ataweg/aweAvrSynth/PCB/Mainboard/avrsynth.sch

## KiCad design PCB/Mainboard/avrsynth.sch (2012-10-20)

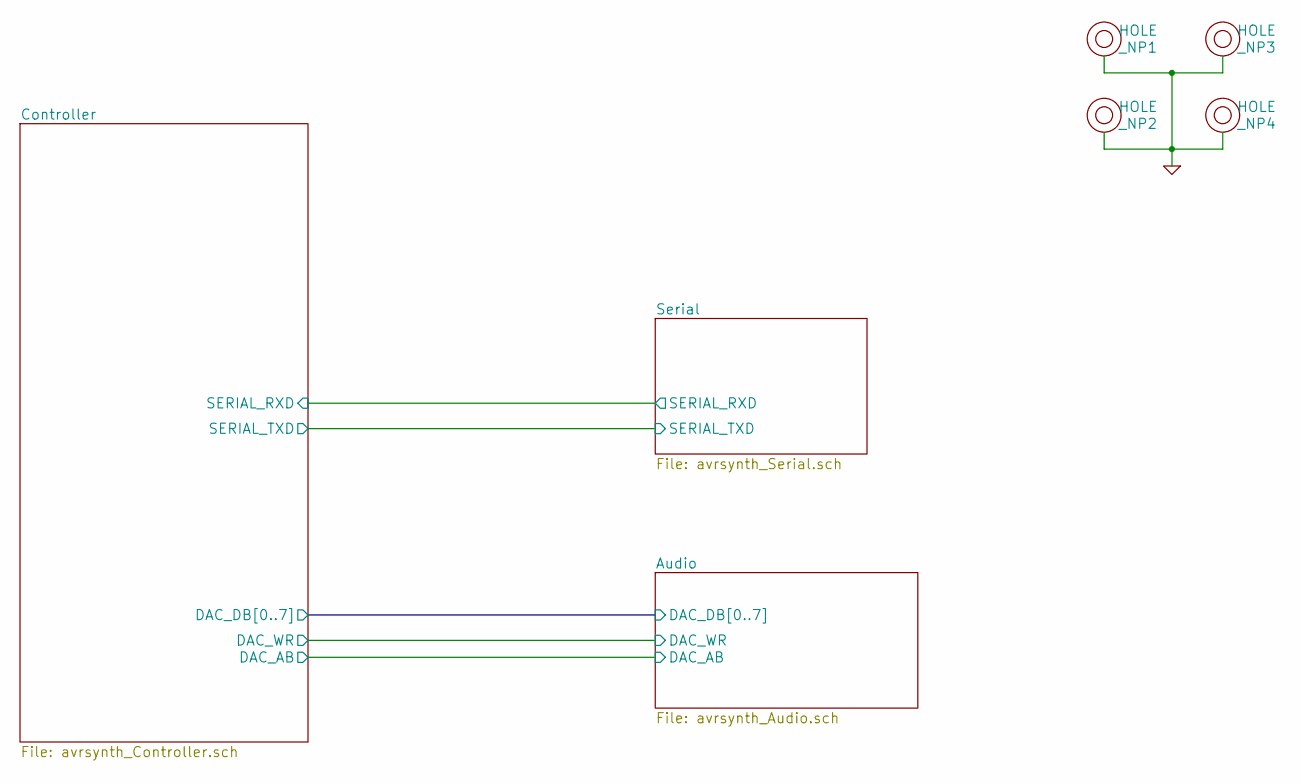
[picture p12: schematic avrsynth.sch]

Parts:
_NP1, _NP2, _NP3, _NP4: HOLE; HOLE_32

Connections:
GND: _NP1.1, _NP2.1, _NP3.1, _NP4.1
