ataweg/aweAvrSynth/PCB/Mainboard/avrsynth_Audio.sch

## KiCad design PCB/Mainboard/avrsynth_Audio.sch (2012-10-20)

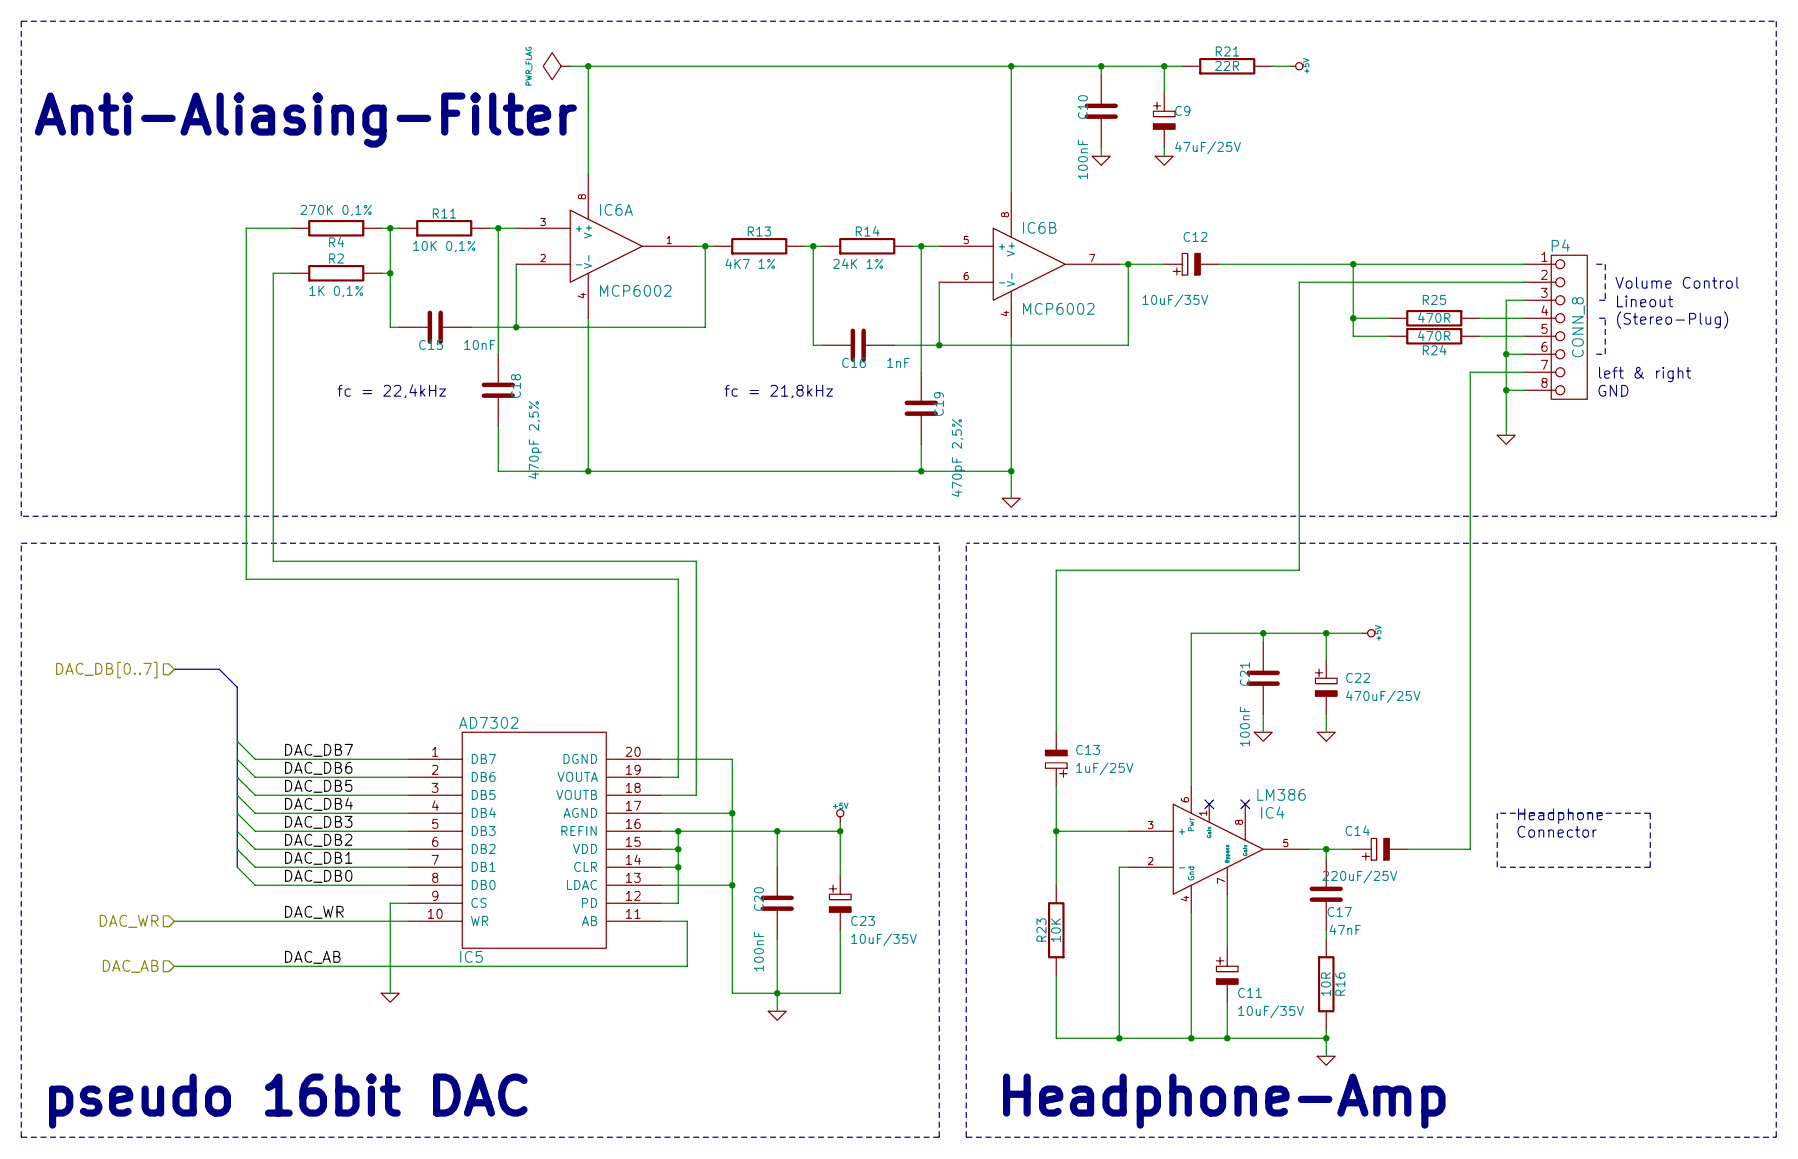
[picture p13: schematic avrsynth_Audio.sch]

Parts:
C9: 47uF/25V; C1V5
C10, C20, C21: 100nF; C2
C11, C12, C23: 10uF/35V; C1V5
C13: 1uF/25V; C1V5
C14: 220uF/25V; C2V8
C15: 10nF; C2
C16: 1nF; C2
C17: 47nF; C2
C18, C19: 470pF 2,5%; C2
C22: 470uF/25V; C2V10
IC4: LM386; DIP-8__300
IC5: AD7302; DIP-20__300
IC6: MCP6002; DIP-8__300
P4: CONN_8; PS25_8G
R2: 1K 0,1%; R4
R4: 270K 0,1%; R4
R11: 10K 0,1%; R4
R13: 4K7 1%; R4
R14: 24K 1%; R4
R16: 10R; R4
R21: 22R; R4
R23: 10K; R4
R24, R25: 470R; R4

Connections:
+5V: C20.2, C21.2, C22.2 (+), C23.2 (+), IC4.6 (Pwr), IC5.12 (PD), IC5.14 (CLR), IC5.15 (VDD), IC5.16 (REFIN), R21.2
DAC_AB: IC5.11 (AB)
DAC_DB0: IC5.8 (DB0)
DAC_DB1: IC5.7 (DB1)
DAC_DB2: IC5.6 (DB2)
DAC_DB3: IC5.5 (DB3)
DAC_DB4: IC5.4 (DB4)
DAC_DB5: IC5.3 (DB5)
DAC_DB6: IC5.2 (DB6)
DAC_DB7: IC5.1 (DB7)
DAC_WR: IC5.10 (WR)
GND: C9.1 (-), C10.1, C11.1 (-), C18.1, C19.1, C20.1, C21.1, C22.1 (-), C23.1 (-), IC4.2 (-), IC4.4 (Gnd), IC5.9 (CS), IC5.13 (LDAC), IC5.17 (AGND), IC5.20 (DGND), IC6.4 (V-), P4.3, P4.6, P4.8, R16.2, R23.1
unnamed: C9.2 (+), C10.2, IC6.8 (V+), R21.1
unnamed: C11.2 (+), IC4.7 (Bypass)
unnamed: C12.1 (-), P4.1, R24.2, R25.2
unnamed: C12.2 (+), C16.1, IC6.6 (-), IC6.7
unnamed: C13.1 (-), P4.2
unnamed: C13.2 (+), IC4.3 (+), R23.2
unnamed: C14.1 (-), P4.7
unnamed: C14.2 (+), C17.2, IC4.5
unnamed: C15.1, IC6.1, IC6.2 (-), R13.1
unnamed: C15.2, R2.2, R4.1, R11.1
unnamed: C16.2, R13.2, R14.1
unnamed: C17.1, R16.1
unnamed: C18.2, IC6.3 (+), R11.2
unnamed: C19.2, IC6.5 (+), R14.2
unnamed: IC5.18 (VOUTB), R2.1
unnamed: IC5.19 (VOUTA), R4.2
unnamed: P4.4, R25.1
unnamed: P4.5, R24.1

Notes on the sheet:
fc = 21,8kHz
fc = 22,4kHz
Headphone Connector
left & right
GND
Headphone-Amp
pseudo 16bit DAC
Anti-Aliasing-Filter
Volume Control
Lineout (Stereo-Plug)
