ataweg/aweAvrSynth/PCB/Mainboard/avrsynth_Controller.sch

## KiCad design PCB/Mainboard/avrsynth_Controller.sch (2012-10-20)

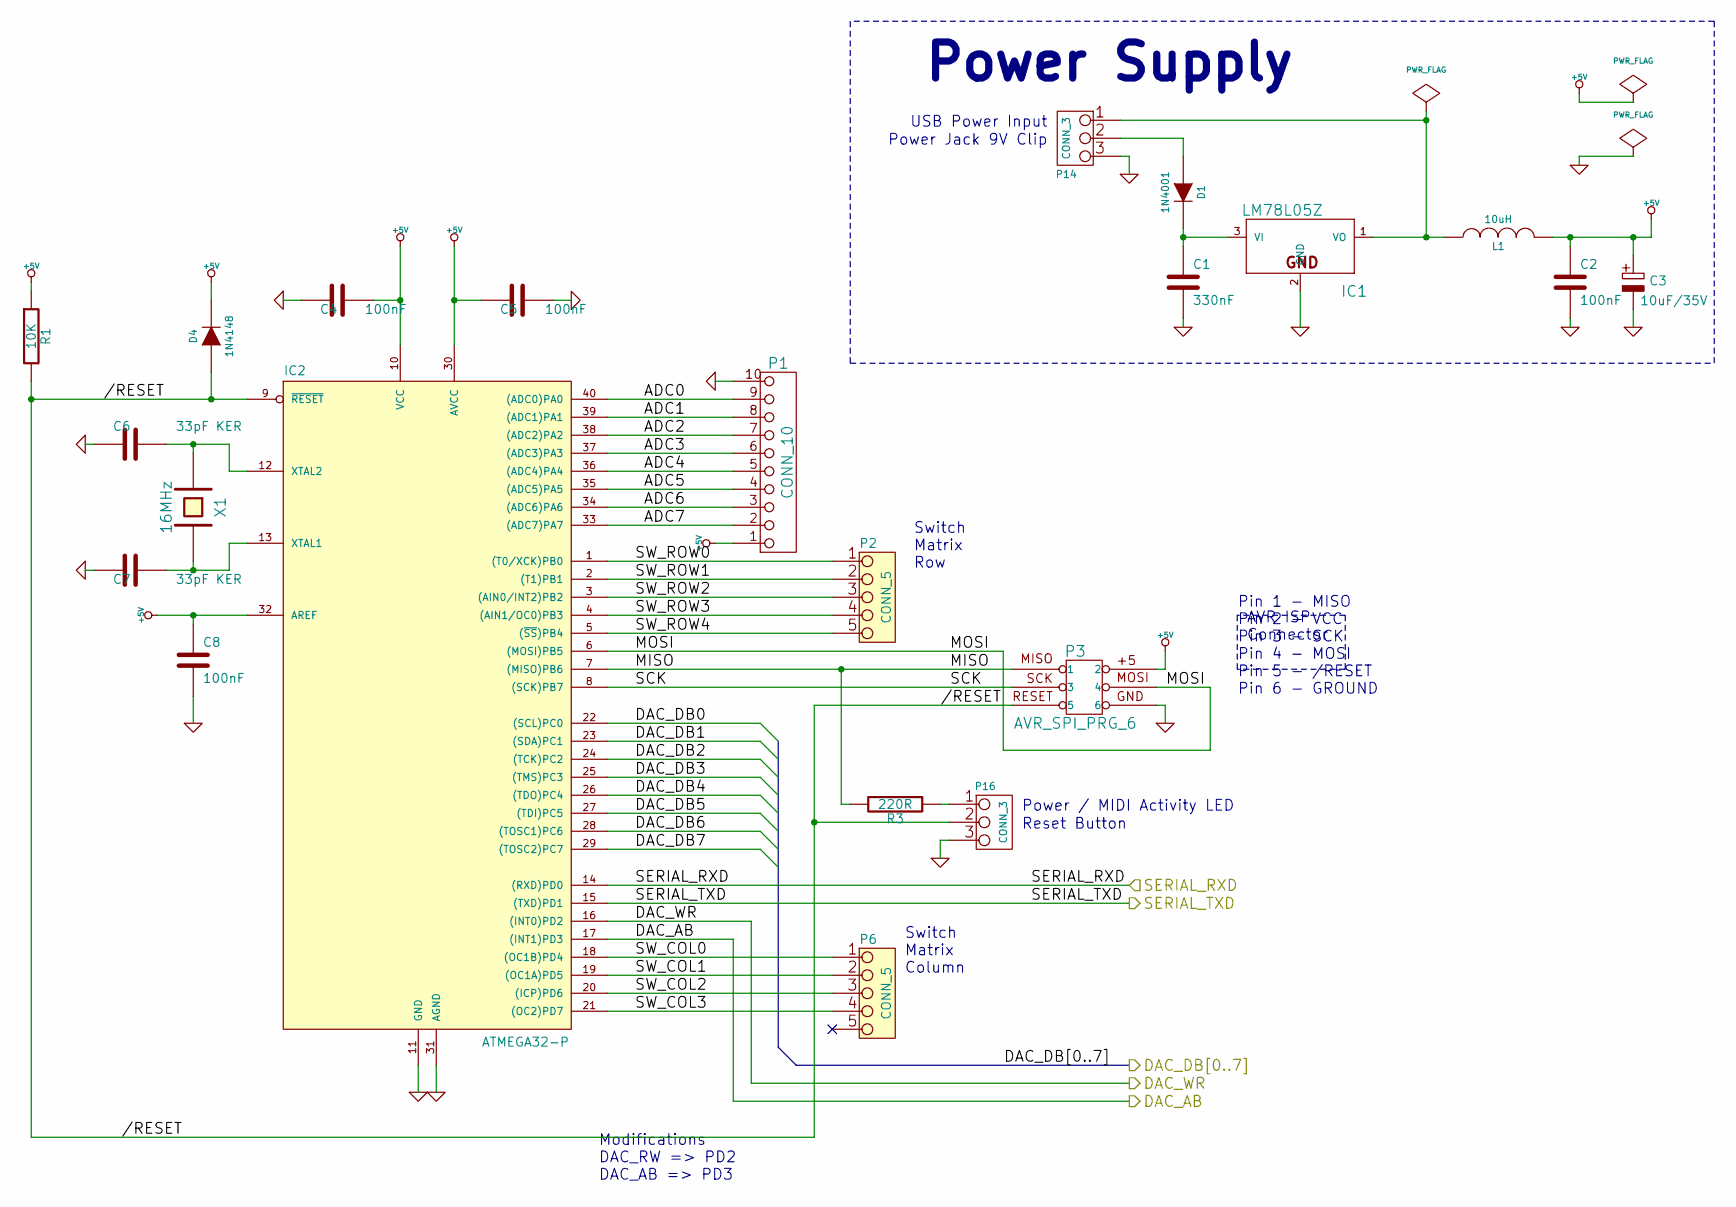
[picture p14: schematic avrsynth_Controller.sch]

Parts:
C1: 330nF; C2
C2: 100nF; C2
C3: 10uF/35V; C1V5
C4, C5, C8: 100nF; C1
C6, C7: 33pF KER; C1
D1: 1N4001; DO41-4
D4: 1N4148; DO35-3
IC1: LM78L05Z; TO92-123
IC2: ATMEGA32-P; DIP-40__600
L1: 10uH; R5
P1: CONN_10; PS25_10G
P2, P6: CONN_5; PS25_5G
P3: AVR_SPI_PRG_6
P14, P16: CONN_3; PS25_3G
R1: 10K; R4
R3: 220R; R4
X1: 16MHz; HC-49V

Connections:
+5V: C2.1, C3.2 (+), C4.1, C5.2, C8.1, D4.2 (K), IC2.10 (VCC), IC2.30 (AVCC), IC2.32 (AREF), L1.2, P1.1, P3.2, R1.1
/RESET: D4.1 (A), IC2.9 (~RESET), P3.5, P16.2 (PM), R1.2
ADC0: IC2.40 ((ADC0)PA0), P1.9
ADC1: IC2.39 ((ADC1)PA1), P1.8
ADC2: IC2.38 ((ADC2)PA2), P1.7
ADC3: IC2.37 ((ADC3)PA3), P1.6
ADC4: IC2.36 ((ADC4)PA4), P1.5
ADC5: IC2.35 ((ADC5)PA5), P1.4
ADC6: IC2.34 ((ADC6)PA6), P1.3
ADC7: IC2.33 ((ADC7)PA7), P1.2
DAC_AB: IC2.17 ((INT1)PD3)
DAC_DB0: IC2.22 ((SCL)PC0)
DAC_DB1: IC2.23 ((SDA)PC1)
DAC_DB2: IC2.24 ((TCK)PC2)
DAC_DB3: IC2.25 ((TMS)PC3)
DAC_DB4: IC2.26 ((TDO)PC4)
DAC_DB5: IC2.27 ((TDI)PC5)
DAC_DB6: IC2.28 ((TOSC1)PC6)
DAC_DB7: IC2.29 ((TOSC2)PC7)
DAC_WR: IC2.16 ((INT0)PD2)
GND: C1.2, C2.2, C3.1 (-), C4.2, C5.1, C6.2, C7.2, C8.2, IC1.2 (GND), IC2.11 (GND), IC2.31 (AGND), P1.10, P3.6, P14.3, P16.3
MISO: IC2.7 ((MISO)PB6), P3.1, R3.2
MOSI: IC2.6 ((MOSI)PB5), P3.4
unnamed: C1.1, D1.2 (K), IC1.3 (VI)
unnamed: C6.1, IC2.12 (XTAL2), X1.1
unnamed: C7.1, IC2.13 (XTAL1), X1.2
unnamed: D1.1 (A), P14.2 (PM)
unnamed: IC1.1 (VO), L1.1, P14.1
unnamed: P16.1, R3.1
SCK: IC2.8 ((SCK)PB7), P3.3
SERIAL_RXD: IC2.14 ((RXD)PD0)
SERIAL_TXD: IC2.15 ((TXD)PD1)
SW_COL0: IC2.18 ((OC1B)PD4), P6.1
SW_COL1: IC2.19 ((OC1A)PD5), P6.2
SW_COL2: IC2.20 ((ICP)PD6), P6.3
SW_COL3: IC2.21 ((OC2)PD7), P6.4
SW_ROW0: IC2.1 ((T0/XCK)PB0), P2.1
SW_ROW1: IC2.2 ((T1)PB1), P2.2
SW_ROW2: IC2.3 ((AIN0/INT2)PB2), P2.3
SW_ROW3: IC2.4 ((AIN1/OC0)PB3), P2.4
SW_ROW4: IC2.5 ((~SS~)PB4), P2.5

Notes on the sheet:
Switch Matrix Column
Switch Matrix Row
Modifications DAC_RW => PD2 DAC_AB => PD3
Power / MIDI Activity LED
Reset Button
Power Supply
Power Jack 9V Clip
USB Power Input
Pin 1 - MISO Pin 2 - VCC Pin 3 - SCK Pin 4 - MOSI Pin 5 - /RESET Pin 6 - GROUND
AVR ISP Connector
