ataweg/aweAvrSynth/PCB/Mainboard/avrsynth_Serial.sch

## KiCad design PCB/Mainboard/avrsynth_Serial.sch (2012-10-20)

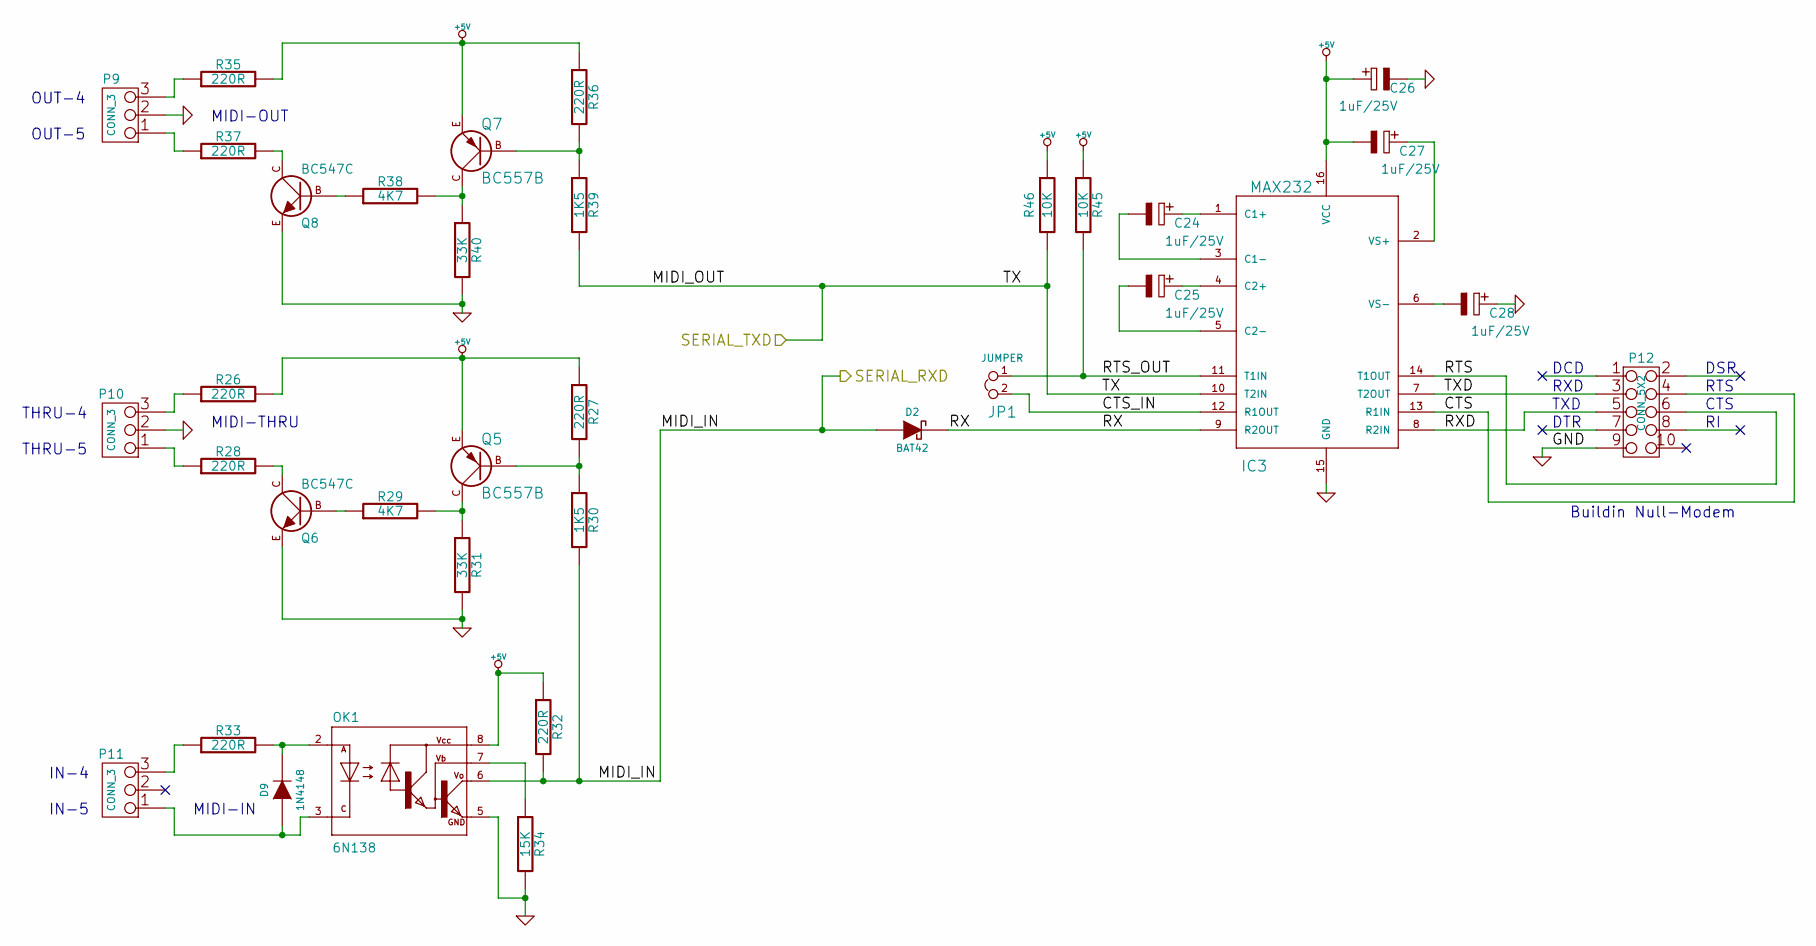
[picture p15: schematic avrsynth_Serial.sch]

Parts:
C24, C25, C26, C27, C28: 1uF/25V; C1V5
D2: BAT42; DO35-3
D9: 1N4148; DO35-3
IC3: MAX232; DIP-16__300
JP1: JUMPER; pin_array_2x1
OK1: 6N138; DIP-8__300
P9, P10, P11: CONN_3; PS25_3G
P12: CONN_5X2; pin_array_5x2
Q5, Q7: BC557B; TO92
Q6, Q8: BC547C; TO92
R26, R27, R28, R32, R33, R35, R36, R37: 220R; R4
R29, R38: 4K7; R4
R30, R39: 1K5; R4
R31, R40: 33K; R4
R34: 15K; R4
R45, R46: 10K; R4

Connections:
+5V: C26.2 (+), C27.1 (-), IC3.16 (VCC), OK1.8 (VCC), Q5.E, Q7.E, R26.2, R27.1, R32.1, R35.2, R36.1, R45.1, R46.1
CTS: IC3.13 (R1IN), P12.4
CTS_IN: IC3.12 (R1OUT), JP1.2
GND: C26.1 (-), C28.2 (+), IC3.15 (GND), OK1.5 (GND), P9.2 (PM), P10.2 (PM), P12.9, Q6.E, Q8.E, R31.2, R34.2, R40.2
MIDI_IN: D2.1 (A), OK1.6 (VO), R30.2, R32.2
MIDI_OUT: IC3.10 (T2IN), R39.2, R46.2
unnamed: C24.1 (-), IC3.3 (C1-)
unnamed: C24.2 (+), IC3.1 (C1+)
unnamed: C25.1 (-), IC3.5 (C2-)
unnamed: C25.2 (+), IC3.4 (C2+)
unnamed: C27.2 (+), IC3.2 (VS+)
unnamed: C28.1 (-), IC3.6 (VS-)
unnamed: D9.1 (A), OK1.3 (C), P11.1
unnamed: D9.2 (K), OK1.2 (A), R33.2
unnamed: OK1.7 (VB), R34.1
unnamed: P9.1, R37.1
unnamed: P9.3, R35.1
unnamed: P10.1, R28.1
unnamed: P10.3, R26.1
unnamed: P11.3, R33.1
unnamed: Q5.B, R27.2, R30.1
unnamed: Q5.C, R29.2, R31.1
unnamed: Q6.B, R29.1
unnamed: Q6.C, R28.2
unnamed: Q7.B, R36.2, R39.1
unnamed: Q7.C, R38.2, R40.1
unnamed: Q8.B, R38.1
unnamed: Q8.C, R37.2
RTS: IC3.14 (T1OUT), P12.6
RTS_OUT: IC3.11 (T1IN), JP1.1, R45.2
RX: D2.2 (K), IC3.9 (R2OUT)
RXD: IC3.8 (R2IN), P12.5
TXD: IC3.7 (T2OUT), P12.3

Notes on the sheet:
OUT-4
OUT-5
IN-5
IN-4
THRU-5
THRU-4
Buildin Null-Modem
CTS
RTS
DSR
DTR
RXD
TXD
DCD
MIDI-IN
MIDI-THRU
MIDI-OUT
