ataweg/aweAvrSynth/PCB/Wiring/avrsynth_Wiring.sch

## KiCad design PCB/Wiring/avrsynth_Wiring.sch (2012-10-20)

Schematic: avrsynth_Wiring.sch

Parts:
C1: 10uF/35V; C1V5
C2: 100nF; C2
D1: LED red; LED_5mm
D3, D4, D5, D6, D7, D8, D9, D10, D11, D12, D13, D14, D15, D16, D17, D18, D19, D20, D21, D22: 1N4148; DO35-3
E1, E2, E3, E4, E5, E6, E7, E8: KNOPF 14M-4 SW
E9: KNOPF 20M-4 SW
E11, E12, E13, E14, E15, E16, E17, E18: DECKEL 14M BL
E19: DECKEL 20M RT
E21, E22, E23, E24, E25, E26, E27, E28: ZEIGER 14-1 SW
E29: ZEIGER 20-1 SW
E33: Flachbandkabel 10-polig 30cm
E34: 10-pol Schneidklemm-Buchse
E35: Gehäuse
E36: IC Fassungen
J1: JACK-STEREO 6.35; Jack-6.35-Stereo
J2: JACK_2P
J3: JACK-STEREO-SW 3.5; Jack-3.5-Stereo-SW
J4: JACK-STEREO-SW 6.35; Jack-6.35-Stereo-SW
J5: USB_2
P1: SUBD-F09D
P2, P3, P4: DIN-BUCHSE-5POL
P5: 9V-BATTERIE-CLIP
P6: CONN_5X2
RV1, RV2, RV3, RV4, RV5, RV6, RV7, RV8: 47K LIN; poti_4mm
RV9: 47K LOG; poti_4mm
SW1, SW2, SW3, SW4, SW5, SW6, SW7, SW8, SW9, SW10, SW11, SW12, SW13, SW14, SW15, SW16: SWITCH_INV; Kippschalter
SW17: KDR16
SW18: PHAP-3301
_P1: CONN_10
_P2, _P6: CONN_5
_P4: CONN_8
_P9, _P10, _P11, _P13, _P16: CONN_3

Notes on the sheet:
PD7
PD6
PD5
PD4
PB4
PB3
PB2
PB1
PB0
Volume Control
Reset- Button
VCC
GND
SWITCHES
-->
<--
LED
Power / MIDI Activity LED
ADC
Power
Serial
Audio
MIDI-OUT
MIDI-THRU
MIDI-IN
Lineout Jack 6,35 mm
Headphone Jack 3,5 mm
Headphone Jack 6,35 mm
Anschlüße für - Stromversorgung - Headphone 6,35 mm - Headphone 3,5 mm - Lineoout - DIN-Buchsen für Mdi-In Midi-Out Midi-Thru - RS-232 Sub-D 9pol - Lautsprecher - Poti für Lautstärke - Umschalter Midi/Serial
Lineout (Stereo-Plug)
Headphone Connector
left & right
