ataweg/aweAvrSynth/Firmware/aweMeeblipSE-v3.asm

;----------------------------------------------------------------------------
; configure build
;----------------------------------------------------------------------------

; set default values for aweMeeblipSE_V2.04 code for avrSynth hardware with uart support

	.set	MEEBLIP_V1_31_HW	= 0	; 0: use my cloned&modified pcb version 1.27
	.set	MEEBLIP_MICRO_V2_04_HW	= 0	; dto.

	.set	USE_SERIAL_OUT		= 1 & !MEEBLIP_V1_31_HW & !MEEBLIP_MICRO_V2_04_HW
	.set	USE_DEBUG_OUT		= 1 & USE_SERIAL_OUT

	.set	MEEBLIP_VERSION		= 303

;----------------------------------------------------------------------------
; process defines from command line
; valid defines are:
;  _MEEBLIP_V1_31_HW
;  _MEEBLIP_MICRO_V2_04_HW
;  _USE_SERIAL_OUT
;  _USE_DEBUG_OUT
;----------------------------------------------------------------------------

#if defined( _MEEBLIP_V1_31_HW)
	.set	MEEBLIP_V1_31_HW	= _MEEBLIP_V1_31_HW
#endif

#if defined( _MEEBLIP_MICRO_V2_04_HW)
	.set	MEEBLIP_MICRO_V2_04_HW	= _MEEBLIP_MICRO_V2_04_HW
#endif

#if defined( _USE_SERIAL_OUT)
	.set	USE_SERIAL_OUT		= _USE_SERIAL_OUT & !MEEBLIP_V1_31_HW & !MEEBLIP_MICRO_V2_04_HW
#else
	.set	USE_SERIAL_OUT		=  USE_SERIAL_OUT & !MEEBLIP_V1_31_HW & !MEEBLIP_MICRO_V2_04_HW
#endif

#if defined( _USE_DEBUG_OUT)
	.set	USE_DEBUG_OUT		= _USE_DEBUG_OUT & !MEEBLIP_V1_31_HW & !MEEBLIP_MICRO_V2_04_HW
#else
	.set	USE_DEBUG_OUT		=  USE_DEBUG_OUT & USE_SERIAL_OUT
#endif

;----------------------------------------------------------------------------
;
; based on meeblip se V2.04 source code
;
; Axel Werner
;
; requires asm2 assembler, asm leads to some undefined variable errors
;
;----------------------------------------------------------------------------
; Todo
;			* prevent wrong serial out when changing baudrate
;			* send debug messages as sys control
;
;			* arpeggiator: play a captured or preloaded sequence of notes
;
;----------------------------------------------------------------------------
; Changelog
;
; 2013.02.13	AWe	new option: play arpeggiator notes only once
;                       capture all notes, discard oldest note in buffer, if buffer is full
;			start release phase also for filter envelope generator when key is released.
; 2013.02.08	AWe	remove gaps in NOTES_BUFFER in any case
;			move startup initialisation to end of code block
;			use new TIMETORATE table with 64 or 128 values
; 2013.02.04	AWe	aweMeeblipSE_V3.03.asm
;			add arpeggiator (inspired by code from Daniel Kruszyna)
;			* new switches: DISTORTION => LFO_ENABLE, ARP_REPEAT => DISTORTION, ARP_ENABLE => FILTER_MODE
;			* new knobs: ARP_RATE => upper OSC_B_DETUNE, ARP_THRESHOLD => PWM_WITDH
;----------------------------------------------------------------------------
; 2013.01.20	AWe	fix midi out value range to 0..127
; 2012.11.16	AWe	switch to enable/disable debug mode, send midi cc
; 2012.11.14	AWe	ADC-Filter, to prevent LSB toggling
;			inhibit midi out for switches when used as input for button commands
; 2012.11.06	AWe	Add midi out for knobs and switches (send on change)
;			using an interrupt driven serial output with a buffer of 16 or more bytes
;			sending a byte needs 320us, so a 3 byte change coontrol message requires 1 ms to transmit
; 2012.10.19	AWe	let the oscillator running, but stop it when there is no VCA output
; 2012.10.12	AWe	add support for meeblip-micro
;			- Assign individual switches instead of switch matrix
;			- Synthesis engine defaults to MIDI channel 1
; 2012.10.09	AWe	reorder switches in PATCH_SWITCH4
;			reorder parameter in midi controls CC14..CC19
;			synchronize PULSE_KNOB with LFO2FREQ and vice versa
;			use c-style defines
; 2012.10.04	AWe	fix mixer bug: OCSB disabled and balance is at left stop, then there was no sound
; 2012.10.03	AWe	update ADSR parameter with knob values from midi only when they are greater zero
; 2012.09.17	AWe	swap sliders for DCA and DCA
; 2012.09.11	AWe	add switch to enable midi velocity to dcf (SW_VELOCITY)
; 2012.09.10	AWe	bug fix: don't save PATCH_SWITCH, when a button is pressed
; 2012.08.16	AWe	move MASTER_VOLUME control to mainloop
; 2012.08.09	AWe	giveup to build meeblip original code
;			USE_MORE_SWITCHES, USE_EXTENDED_BUTTON_FUNCTIONS, USE_EXTENDED_MIDI_CONTROL,
;			USE_EXTENDED_PATCH, USE_MASTER_VOLUME_EXT
;----------------------------------------------------------------------------
; 2012.06.07	AWe	correct typo
; 2012.04.05	AWe	update uart startup message to version 2.04 and (c) AWe 2012)
; 2012.01.15	AWe	adjust Q_OFFSET, correct patches, update changed midi cc assignment
; 2012.01.09	AWe	integrate changes from meeblip-se-v2.asm (V2.04 2012.01.05) from James Grahame
;			(create a new version aweMeeblipSE_V2.04.asm)
;			remove code parts previously controlled by the option switches
;			* USE_ORIGINAL_MUL32X16, USE_ORIGINAL_MUL8X8S, USE_ORIGINAL_DCA,
;			* USE_OSCBOFF_LEVEL_CORRECTION, USE_ORIGINAL_WAVETABLES, USE_ORIGINAL_BANDLIMITED_PWM,
;			* USE_BANDLIMITED_DCO_A, USE_BANDLIMITED_DCO_B, USE_ORIGINAL_TAB_VCA
;			set Q_OFFSET to 8, previous value was 24
;			remove patch switch for SW_OSCA_WAVE_SIN and SW_OSCB_WAVE_SIN
;			correct LED flash frequency for extended button functions
;			correct some typos
; 2012.01.04	AWe	use better rounding for calculated table TAB_VCF
;			move calculation of scaled_resonance from isr to mainloop
;			change q offset from 32 to 24, lower values will cause clipping
;			change index of some midi cc
;			change bit SW_MIX_RING position of in variable PATCH_SWITCH3
;			for extended button functions let LED blink faster
; 2011.12.22	AWe	bugfix: using of option USE_INIT_ENV_GENERATORS can cause hearable clicks, so don't use it
;			bugfix: correct routine mul32x16 with hw multiplier and in volume control function
;			bugfix: use mulsu for LFO modulation and keybard tracking
;			for LFO2 change Amin to 0 and Amx to 255, because wee have a PWM_DEPTH control via MIDI
;			add more sample patches to the eeprom
; 2011.12.15	AWe	integrate bugfixes on meeblip-se-v2.asm (V2.02 2011.12.13) from James Grahame
;			I found and reported these bugfixes ;-)
;			save/load more midi cc parameter to eeprom (enhanced patches) (USE_EXTENDED_PATCH)
;			remove limits of RESONANCE knob, now no limits 0..254 (USE_ORIGINAL_RESONANCE_LIMIT)
;			correct limits of PULSE_KNOB, PULSE_KNOB_LIMITED, now 4..127 (USE_ORIGINAL_PWM_LIMIT)
;			optimize usage of "lpm" opcode; hint: "lpm" has not the same opcode like "lpm r0,z"
;			use patch 0 as a default patch, it is save for over writing (USE_READ_ONLY_PATCH_ZERO)
;			in DCA function use a HW-multipier, not the shift-and-add algorithm for the
;			   16s*8u multiplication (USE_ORIGINAL_DCA)
;			update env parameter from midi-cc or switches and knobes (USE_ORIGINAL_ENVELOPE_CONTROL)
;			map ATTACKTIME, ATTACKTIME2 to KNOB_AMP_ATTACK, KNOB_DCF_ATTACK and vice versa (USE_ORIGINAL_ENVELOPE_CONTROL)
;			level adjustment, when osc b is off (USE_OSCBOFF_LEVEL_CORRECTION)
;			master volume control - VOLUME 0..254 or -36db..+12db (USE_MASTER_VOLUME)
;			redesign PWM signal generation without using falling sawtooth waveform (USE_ORIGINAL_BANDLIMITED_PWM)
;			mixer balance also for ringmodulator input (USE_RINGMODULATOR_BALANCE)
; 2011.12.11	AWe	integrate changes from meeblip-se-v2.asm (V2.01 2011.12.01) from James Grahame
;			(create a new version aweMeeblipSE_V2.01.asm)
;			add eeprom content for patch 0
;			correct some bugs
;			* when osc b is disabled, set its output value to zero, not to $80
;			* save mixer output value (r16) to OSC_OUT_L after scaling down
;			* initialize some sound parameter with zero instead of 255
;			* after power on force processing the key changes by set the old state to the
;			  inverted value of the current switch state
;			adjust ringmodulator output level
; 2011.12.07	AWe	improve output level of mixer
;			recalculate bandlimited waveform so that they have the same average amplitude
;			 now we have 12 subtables for each waveform; one subtable is used for 8 notes
;			osc A and osc B use their own WAVETABLE variable
;			remove dco_fm
;			replace switch "osc fm" and "bandlimited osc" with "mixer ringmodulator" and "transpose"
; 2011.12.03	AWe	use DCOs from avrSynth, but without sine waveform
;			fix bug: adjust level of pwm waveform by adding a duty cycle depend offset
;			change slope of wavetable sawtooth from falling to rising
; 2011.11.29	AWe	add Ringmodulator
;			change mixer
;			use improved noise generator
;			add more switches, controlled thru midi cc $50..$5F
;			add midi cc for contolling some sound parameter
;			correct bug: msb of midi cc data is bit 6, not bit 7
;			use FMDEPTH to control the dco A fm modulation
;			initialize varibales RESONANCE, PORTAMENTO, ENV_FRAC_L2, ENV_FRAC_H2, ENV_INTEGR2, ENVPHASE2,
;			read some sound paramters for eeprom during startup: LFO2FREQ, PWMDEPTH, DCOA_LEVEL, DCOB_LEVEL
;			correct bug: SW_SUSTAIN did only work when SW_KNOB_SHIFT is set to upper
;			remove dead code
;			set Amax for LFO2 to 255, previos value was 100
;			add features from LFO also to LFO2
;			correct sustain level after decay is done
;			clear env variables when envelope starts
;			add "transpose" and keyboard tracking switch
;			use modified dcf amount control with range -128..+127
;			add dca mode switch 0 (gate), 1 (env)
; 2011.11.24	AWe	code beautification, replace blanks with tabs (tab width is 8)
;			add more comments
;			comment/define out useless opcodes, search "; (1)"
;			optimize function TAB_BYTE, value returned now in r16
;			optimize access to program memory in functions LOAD_32BIT, TAB_WROD
;
; Adaptions to my avrSynth Hardware
; 2011.11.06	AWe	move LED from Atmega pin PD1 to PB6
; 2011.09.06	AWe	invert state of switches
; 2011.08.19	AWe	swap ATmega32 pins: DAC_RW/PD2 with DAC_AB/PD3
;
;----------------------------------------------------------------------------
;                     _     _  _
;                    | |   | |(_)
;   ____  _____ _____| |__ | | _ ____      ___ _____
;  |    \| ___ | ___ |  _ \| || |  _ \    /___) ___ |
;  | | | | ____| ____| |_) ) || | |_| |  |___ | ____|
;  |_|_|_|_____)_____)____/ \_)_|  __/   (___/|_____)
;                             |_|
;
;   meeblip se V2 - the hackable digital synthesiser
;
;	For Version 2.0 Meeblip hardware (with save/load switches and patch memory)
;
;----------------------------------------------------------------------------
;
; Changelog
;
; V2.04 2012.01.05	- Added maximum resonance table
;			- Envelopes no longer restart on note off release if they're stopped
;			- Replace MUL8X8S routine with hardware multiply
;			- Updated LPM calls throughout code
;			- Implement 2 byte offsets for all table lookups
;			- New bandlimited waveforms with matched average amplitude (Axel Werner)
;			- New 32x16 bit multiply, 32 bit load (AW)
;			- Use signed multiply in DCA (AW)
;			- New oscillator mix routine (AW)
;			- New TAB_VCF, TAB_VCA and TIMETORATE tables (AW)
;			- Fix envelope decay bug (AW)
; V2.03 2011.12.20	- Added MIDI Velocity to VCF Envelope Modulation
;			- Changed maximum resonance and resonance scaling limits
;			- Updated oscillator mix levels because of mix clipping
; V2.02 2011.12.12	- Corrected code to save pre-filtered waveform
; V2.01 2011.12.01	- Added inverse sawtooth waveform
;			- Fixed wavetable overflow in variable pulse calculation
;			- Increase Portamento rate
;			- Enable patch load/save and MIDI save functions (careful with V1 hardware - you have to use the DIP switches)
;			- Increase Portamento rate
;			- Debugged MIDI CC switch loading routine
;			- Removed unnecessary opcodes throughout code
; V2.00 2011.11.23	- Bandlimited pulse and PWM wave built from out-of-phase ramps
;			- Bandlimited square, saw and triangle oscillators
;			- Patch state engine (independent of front panel controls)
;			- New knob scan routine (scans only the most recently converted analog channel)
;			- Dual ADSD envelopes
;			- PWM sweep switch and PWM rate knob (limited between 0-50% pulse duty cycle)
;			- Filter envelope amount knob added
;			- MIDI control of all parameters
;			- Reorganized front panel
;			- MIDI knob and switch CC control
;			- DCA gate, LFO sync, modulation wheel and filter key track now always on
;			- LFO enable switch added
;			- anti-alias switch added - off uses bandlimited wave 0, on uses bandlimited wavetable 0..15, based on note
;			- Added variable names for switches instead of using bit ops - allows easier reorganization of panel
;			- FM switch - off or 100%
;			- New sample rate - 36363.63636 Hz, approximately 440 instructions per sample
; V1.05 2011.02.04	- Save dual parameter knob values to eeprom and reload on power up.
; V1.04 2011.01.19	- MIDI CC RAM table added.
;			- PWM waveform with dedicated fixed sweep LFO
;			- 8-bit multiplies optimized in main loop
;			- LFO Sync switch now retriggers LFO on each keypress
;			- Initialize FM Depth to zero on power up
; V1.03			- VCA and VCF level tables extended to reduce stairstepping
; V1.02			- Flip DAC write line high immediately after outputting sample
; V1.01			- Optimized DCOA+DCOB summer, outputs signed value
; V1.00			- Power/MIDI status LED remains on unless receiving MIDI
;			- Sustain level of ADSR envelope is exponentially scaled
;			- Non-resonant highpass filter implemented
;			- Filter Q level compensation moved outside audio sample calc interrupt
;			- Filter calculations increased to 16x8-bit to reduce noise floor
;			- DCA output level calculations are rounded
;			- Mod wheel no longer overrides LFO level knob when less than knob value
; V0.90			- Initial release
;
;----------------------------------------------------------------------------
;
;	MeeBlip Contributors
;
;	Jarek Ziembicki - Created the original AVRsynth, upon which this project is based.
;	Laurie Biddulph - Worked with Jarek to translate his comments into English, ported to Atmega16
;	Daniel Kruszyna - Extended AVRsynth (several of his ideas are incorporated in MeeBlip)
;	Julian Schmidt  - Original filter algorithm
;	Axel Werner	- Code optimization, bug fixes and new bandlimited waveforms
;	James Grahame   - Ported and extended the AVRsynth code to MeeBlip hardware.
;
;----------------------------------------------------------------------------
;
;	Port Mapping
;
;	PA0..7		8 potentiometers
;	PB0-PB4		Control Panel Switches - ROWS
;	PB5-PB7		ISP programming header
;	PB7		DAC LDAC signal (load both DAC ports synchronously)
;	PC0-PC7		DATA port for DAC
;	PD0		RxD (MIDI IN)
;	PD1		Power ON/MIDI LED
;	PD2		Select DAC port A or B
;	PD3		DAC Write line
;	PD4-PD7		Control Panel Switches - COLUMNS
;
;	Timers
;
;	Timer0		not used
;	Timer1		Time counter: CK/400      --> TCNT1
;	Timer2		Sample timer: (CK/8) / 32 --> 36363.63636 Hz
;
;----------------------------------------------------------------------------

	.nolist
	.include "m32def.inc"
	.list
;	.listmac

;----------------------------------------------------------------------------
;
;----------------------------------------------------------------------------

	.equ	USE_ORIGINAL_DCO_FM		= 1
	.equ	USE_ORIGINAL_RAW_OSC		= 1	; 0: use switch for Ringmodulator enable, set SW_ANTI_ALIAS to 1
	.equ	USE_ORIGINAL_MIXER_LEVEL	= 1	; 0: 6 db more output level, 1: (recommended)

	.equ	USE_TIMETORATE_64		= 0
	.equ	USE_TIMETORATE_128		= 1
	.equ	USE_ARP_TIMETORATE_128		= 1

	.equ	USE_DCA_MOD_SWITCH		= 1
	.equ	USE_EXTENDED_LFO2		= 0	; 1: add waveform selection to lfo2 tri, sqr, random
	.equ	USE_INIT_LFO2			= 1
	.equ	USE_KBD_SYNC			= 1
	.equ	USE_KBD_TRACK_SWITCH		= 1
	.equ	USE_MIDI_FMDEPTH		= 1
	.equ	USE_MIDI_PWMDEPTH		= 1
	.equ	USE_SUSTAIN_UPDATE_ON_NOTE	= 0	; not used yet
	.equ	USE_SYNC_LFO2			= 1
	.equ	USE_TRANSPOSE_SWITCH		= 1	; 1: use DCO_FM switch for transpose

	.equ	USE_MASTER_VOLUME		= 1	; 0: master volume control; 1: control it via MIDI cc
	.equ	USE_READ_ONLY_PATCH_ZERO	= 1	; 0: can overwrite of patch 0, 1: protect patch 0 for overwriting
	.equ	USE_RINGMODULATOR		= 1
	.equ	USE_RINGMODULATOR_BALANCE	= 1
	.equ	USE_ARPEGGIATOR			= 1
	.equ	USE_MIDI_OUT			= 1 & (USE_SERIAL_OUT | USE_DEBUG_OUT)

	.equ	FILL_UP_WITH_DEFAULT_PATCH	= 1

	.equ	Q_OFFSET		= 16
	.equ	PARAM_DEAD_ZONE		= 5
	.equ	ARP_THRESHOLD_MIN	= 8


.if USE_SERIAL_OUT
	.equ	UART_TX_BUFFER_SIZE		= 256			; maximum value
	.equ	UART_TX_BUFFER_MASK		= UART_TX_BUFFER_SIZE - 1
.endif	; USE_SERIAL_OUT

;----------------------------------------------------------------------------
;
;----------------------------------------------------------------------------

	.nolist

.message ""
.message "vvvvvvvvvvvvvvvvvvvvvvvvvvvvvvvvvvvvvvvvvvvvvvvv"

.if MEEBLIP_MICRO_V2_04_HW != 0
  .message "* Build for original Meeblip Micro hardware"
.elif MEEBLIP_V1_31_HW != 0
  .message "* Build for original Meeblip SE hardware"
.else
  .if USE_SERIAL_OUT == 0
    .message "* Build for avrSynth hardware"
  .else
    .message "* Build for avrSynth hardware using uart"
  .endif
.endif

.message "^^^^^^^^^^^^^^^^^^^^^^^^^^^^^^^^^^^^^^^^^^^^^^^^"
.message ""

	.list

;----------------------------------------------------------------------------
;
;----------------------------------------------------------------------------

	.equ	cpu_frequency	= 16000000
	.equ	midi_baud_rate	= 31250
	.equ	KBDSCAN		= 6250

 	.equ	NOTES_BUFFERSIZE= 8	; number of midi notes to remember

.if MEEBLIP_V1_31_HW || MEEBLIP_MICRO_V2_04_HW
	.equ	PORT_MIDI_LED	= PORTD
	.equ	MIDI_LED	= 1	; PD1

	.equ	DAC_AB		= 2	; PD2
	.equ	DAC_WR		= 3	; PD3

	.equ	LOAD_BUTTON	= 2
	.equ	SAVE_BUTTON	= 1
	.equ	MIDI_BUTTON	= 0
.else	; MEEBLIP_V1_31_HW|| MEEBLIP_MICRO_V2_04_HW
	.equ	PORT_MIDI_LED	= PORTB
	.equ	MIDI_LED	= 6	; PB6

	.equ	DAC_WR		= 2	; PD2
	.equ	DAC_AB		= 3	; PD3

	.equ	LOAD_BUTTON	= 1
	.equ	SAVE_BUTTON	= 2
	.equ	MIDI_BUTTON	= 3
.endif	; MEEBLIP_V1_31_HW|| MEEBLIP_MICRO_V2_04_HW

;----------------------------------------------------------------------------
;		V A R I A B L E S   &   D E F I N I T I O N S
;----------------------------------------------------------------------------
; registers:
				; r0	; multiplier result register
				; r1	; dto.

; current phase of DCO A:
	.def	PHASEA_0	= r2	; used in timer0 ISR, not saved on stack
	.def	PHASEA_1	= r3	; dto.
	.def	PHASEA_2	= r4	; dto.

; current phase of DCO B:
	.def	PHASEB_0	= r5	; dto.
	.def	PHASEB_1	= r6	; dto.
	.def	PHASEB_2	= r7	; dto.
; DCF:
	.def	a_L		= r8	; used in timer0 ISR, not saved on stack
	.def	a_H		= r9	; also used in filter, keeps lowpass.

	.def	ZERO		= r10	; the ZERO value
	.def	temp_SREG	= r11

				; r12	; not used
				; r13	; dto.
				; r14	; pre-filter audio
				; r15	; temporary used in ISR, not saved on stack

				; r16	; general purpose, used in ISR, saved on stack
				; r17	; dto.
				; r18	; dto.
				; r19	; dto.
				; r20	; dto.
				; r21	; dto.
				; r22	; dto.
				; r23	; dto.

				; r24	; general purpose
				; r25	; general purpose
				; r26	; general purpose
				; r27	; general purpose
				; r28	; general purpose
				; r29	; general purpose
				; r30	; general purpose, used in ISR, saved on stack
				; r31	; dto.

; RAM (0060h...025Fh):

	.dseg

; MIDI:
MIDIPHASE:		.byte	1
MIDICHANNEL:		.byte	1
MIDIDATA0:		.byte	1
MIDIVELOCITY:		.byte	1
MIDINOTE:		.byte	1
.if !USE_ARPEGGIATOR
MIDINOTEPREV:		.byte	1	; buffer for MIDI note
.else	; !USE_ARPEGGIATOR
MIDINOTE_NEXT:		.byte	1
.endif ; !USE_ARPEGGIATOR
MIDIPBEND_L:		.byte	1	; \
MIDIPBEND_H:		.byte	1	; / -32768..+32766

; current sound parameters:
LFOLEVEL:		.byte	1	; 0..255
KNOB_SHIFT:		.byte	1	; 0= unchanged 255= changed state (not used)
POWER_UP:		.byte	1	; 255 = Synth just turned on, 0 = normal operation
KNOB0_STATUS:		.byte	1	; Each byte corresponds to a panel knob.
KNOB1_STATUS:		.byte	1	; bit 0: 0 = pot not updated since Knob Shift switch change
KNOB2_STATUS:		.byte	1	; 1 = pot has been updated.
KNOB3_STATUS:		.byte	1
KNOB4_STATUS:		.byte	1
KNOB5_STATUS:		.byte	1
KNOB6_STATUS:		.byte	1
KNOB7_STATUS:		.byte	1

SWITCH1:		.byte	1
SWITCH2:		.byte	1
OLD_SWITCH1:		.byte	1	; Previous switch values (used to flag switch changes)
OLD_SWITCH2:		.byte	1

; Switch value currently used (from front panel, MIDI or last loaded patch)
PATCH_SWITCH1:		.byte	1
	.equ	SW_KNOB_SHIFT	= 0	; 0=lower, 1=upper
	.equ	SW_OSC_FM	= 1	; 0=off, 1=on
	.equ	SW_LFO_RANDOM	= 2	; 0=norm, 1=rand
	.equ	SW_LFO_WAVE	= 3	; 0=tri, 1=squ
	.equ	SW_FILTER_MODE	= 4	; 0=lp, 1=hp
	.equ	SW_DISTORTION	= 5	; 0=off, 1=on
	.equ	SW_LFO_ENABLE	= 6	; 0=off, 1=on
	.equ	SW_LFO_DEST	= 7	; 0=DCF, 1=DCO

PATCH_SWITCH2:		.byte	1
	.equ	SW_ANTI_ALIAS	= 0	; 0=off, 1=on
	.equ	SW_OSCB_OCT	= 1	; 0=down, 1=up
	.equ	SW_OSCB_ENABLE	= 2	; 0=off, 1=on
	.equ	SW_OSCB_WAVE	= 3	; 0=saw, 1=squ
	.equ	SW_SUSTAIN	= 4	; 0=ADR, 1=ASR
	.equ	SW_OSCA_NOISE	= 5	; 0=off, 1=on
	.equ	SW_PWM_SWEEP	= 6	; 0=off, 1=LFO2
	.equ	SW_OSCA_WAVE	= 7	; 0=saw, 1=squ

PATCH_SWITCH3:		.byte	1
	.equ	SW_MIX_RING	= 0	; 0=Mixer(default), 1=Ringmodulator
	.equ	SW_VELOCITY	= 1	; 0=off, 1=on
	.equ	SW_DCA_MODE	= 2	; 0=gate, 1=env (default)
	.equ	SW_DCA_OPEN	= 3	; 0=norm, 1=open
	.equ	SW_TRANSPOSE	= 4	; 0=down, 1=up (default)
	.equ	SW_MODWHEEL_ENA	= 5	; 0=diable, 1=enable (default)
	.equ	SW_LFO_KBD_SYNC	= 6	; 0=off, 1=on (default)
	.equ	SW_DCF_KBD_TRACK= 7	; 0=off, 1=on (default)

PATCH_SWITCH4:		.byte	1
	.equ	SW_USER_4_0	= 0	; not used
	.equ	SW_USER_4_1	= 1	; not used
	.equ	SW_ARP_ENABLE	= 2	;
	.equ	SW_ARP_REPEAT	= 3	;
	.equ	SW_USER_4_4	= 4	; not used
	.equ	SW_USER_4_5	= 5	; not used
	.equ	SW_LFO2_WAVE	= 6	; 0=tri, 1=squ
	.equ	SW_LFO2_RANDOM	= 7	; 0=norm, 1=rand

SWITCH3:		.byte	1	; b0: MIDI SWITCH 1
					; b1: MIDI SWITCH 2
					; b2: MIDI SWITCH 3
					; b3: MIDI SWITCH 4

SETMIDICHANNEL:		.byte	1	; selected MIDI channel: 0 for OMNI or 1..15
DETUNEB_FRAC:		.byte	1	; \
DETUNEB_INTG:		.byte	1	; / -128,000..+127,996

NOTE_L:			.byte	1
NOTE_H:			.byte	1
NOTE_INTG:		.byte	1
PORTACNT:		.byte	1	; 2 / 1 / 0: no note / first note / next note
LPF_I:			.byte	1
HPF_I:			.byte	1
LEVEL:			.byte	1	; 0..255
PITCH:			.byte	1	; 0..96
ADC_CHAN:		.byte	1	; 0..7
PREV_ADC_CHAN:		.byte	1	; 0..7
					; Panel knob values.
ADC_0:			.byte	1	;   RESONANCE
ADC_1:			.byte	1	;   CUTOFF
ADC_2:			.byte	1	;   LFOFREQ / KNOB_DCF_DECAY
ADC_3:			.byte	1	;   LFOLEVEL = PANEL_LFOLEVEL / KNOB_DCF_ATTACK = ATTACKTIME2
ADC_4:			.byte	1	;   VCFENVMOD / KNOB_AMP_DECAY
ADC_5:			.byte	1	;   PORTAMENTO / KNOB_AMP_ATTACK = ATTACKTIME
ADC_6:			.byte	1	;   PULSE_KNOB = LFO2FREQ
ADC_7:			.byte	1	;   OSC_DETUNE
OLD_ADC_0:		.byte	1	; Previous panel knob value
OLD_ADC_1:		.byte	1
OLD_ADC_2:		.byte	1
OLD_ADC_3:		.byte	1
OLD_ADC_4:		.byte	1
OLD_ADC_5:		.byte	1
OLD_ADC_6:		.byte	1
OLD_ADC_7:		.byte	1

GATE:			.byte	1	; 0 / 1
GATEEDGE:		.byte	1	; 0 / 1
TPREV_KBD_L:		.byte	1
TPREV_KBD_H:		.byte	1
TPREV_L:		.byte	1
TPREV_H:		.byte	1
DELTAT_L:		.byte	1	; \ Time from former course
DELTAT_H:		.byte	1	; / of the main loop (1 bit = 32 µs)

; 0=stop 1=attack 2=decay 3=sustain 4=release

	.equ	ENV_STOP	= 0
	.equ	ENV_ATTACK	= 1
	.equ	ENV_DECAY	= 2
	.equ	ENV_SUSTAIN	= 3
	.equ	ENV_RELEASE	= 4

ENVPHASE:		.byte	1	; 0=stop 1=attack 2=decay 3=sustain 4=release
ENV_FRAC_L:		.byte	1
ENV_FRAC_H:		.byte	1
ENV_INTEGR:		.byte	1

ENVPHASE2:		.byte	1	; 0=stop 1=attack 2=decay 3=sustain 4=release
ENV_FRAC_L2:		.byte	1
ENV_FRAC_H2:		.byte	1
ENV_INTEGR2:		.byte	1
VELOCITY_ENVMOD:	.byte	1

	.equ	LFOPHASE_RISE	= 0
	.equ	LFOPHASE_FALL	= 1

LFOPHASE:		.byte	1	; 0=up 1=down
LFO_FRAC_L:		.byte	1	; \
LFO_FRAC_H:		.byte	1	;  > -128,000..+127,999
LFO_INTEGR:		.byte	1	; /
LFOVALUE:		.byte	1	; -128..+127

LFO2PHASE:		.byte	1	; 0=up 1=down
LFO2_FRAC_L:		.byte	1	; \
LFO2_FRAC_H:		.byte	1	;  > -128,000..+127,999
LFO2_INTEGR:		.byte	1	; /
LFO2VALUE:		.byte	1	; -128..+127 (currently not used)

OLDWAVEA:		.byte	1
OLDWAVEB:		.byte	1
SHIFTREG_0:		.byte	1	; \
SHIFTREG_1:		.byte	1	;  > shift register for
SHIFTREG_2:		.byte	1	; /  pseudo-random generator
LFOBOTTOM_0:		.byte	1	; \
LFOBOTTOM_1:		.byte	1	;  > bottom level of LFO
LFOBOTTOM_2:		.byte	1	; /
LFOTOP_0:		.byte	1	; \
LFOTOP_1:		.byte	1	;  > top level of LFO
LFOTOP_2:		.byte	1	; /
LFO2BOTTOM_0:		.byte	1	; \
LFO2BOTTOM_1:		.byte	1	;  > bottom level of LFO2
LFO2BOTTOM_2:		.byte	1	; /
LFO2TOP_0:		.byte	1	; \
LFO2TOP_1:		.byte	1	;  > top level of LFO2
LFO2TOP_2:		.byte	1	; /

DCOA_LEVEL:		.byte	1
DCOB_LEVEL:		.byte	1

; increase phase for DCO A
DELTAA_0:		.byte	1
DELTAA_1:		.byte	1
DELTAA_2:		.byte	1

; increase phase for DCO B
DELTAB_0:		.byte	1
DELTAB_1:		.byte	1
DELTAB_2:		.byte	1

; Wavetable select
WAVETABLE_A:		.byte	1	; Bandlimited wavetable 0..11
WAVETABLE_B:		.byte	1	; Bandlimited wavetable 0..11

; oscillator pulse width
PULSE_WIDTH:		.byte	1
PULSE_KNOB_LIMITED:	.byte	1
.if USE_ORIGINAL_DCO_FM
; fm
WAVEB:			.byte	1
.if !USE_MIDI_FMDEPTH
FMDEPTH:		.byte	1
.endif	; !USE_MIDI_FMDEPTH
.endif	; USE_ORIGINAL_DCO_FM

; eeprom
WRITE_MODE:		.byte	1	; 0: enable, 255: disable
WRITE_OFFSET:		.byte	1	; byte 0..15/63 of the patch
WRITE_PATCH_OFFSET_L:	.byte	1	; start of patch in eeprom
WRITE_PATCH_OFFSET_H:	.byte	1	; start of patch in eeprom

; filter
SCALED_RESONANCE:	.byte	1	; not used
b_L:			.byte	1
b_H:			.byte	1
VCF_STATUS:		.byte	1	; 0 indicates VCF off, 1 = on

LFSR_0:			.byte	1	; \
LFSR_1:			.byte	1	;  > linear feedback shift register for
LFSR_2:			.byte	1	; /  noise  generator

.if USE_ARPEGGIATOR
; arpeggiator

	.equ	ARPSTATE_REST		= 0
	.equ	ARPSTATE_NOTEON		= 1
	.equ	ARPSTATE_NOTEOFF	= 2

ARPSTATE:		.byte	1
ARPPHASE_FRAC_L:	.byte	1
ARPPHASE_FRAC_H:	.byte	1
ARPPHASE_INTEGR:	.byte	1
ARPNOTE:		.byte	1	; midi note buffer index

; midi note array
NOTES_BUFFER:		.byte	NOTES_BUFFERSIZE
NOTES_ACTIVE:		.byte	1
.endif ; USE_ARPEGGIATOR

.if USE_SERIAL_OUT
UART_TxHead:		.byte	1
UART_TxTail:		.byte	1
UART_TxBuf:		.byte	UART_TX_BUFFER_SIZE
.endif	; USE_SERIAL_OUT

;----------------------------------------------------------------------------
; MIDI Control Change parameter table
;----------------------------------------------------------------------------
;
; MIDI CC parameters with an offset from MIDICC. They are automatically
; stored for use, just use the variable name to access their value.


MIDICC:	.byte $80
	.equ	MIDIMODWHEEL	= MIDICC + $01

	.equ	LFO2FREQ	= MIDICC + $0E	; Knob 1	14 ; 0..255	 (PULSE_KNOB)
	.equ	PWMDEPTH	= MIDICC + $0F	; Knob 2	15 ; 0..255	 (=LFO2LEVEL)
	.equ	FMDEPTH		= MIDICC + $10	; Knob 3	16 ; 0..255
	.equ	MIDI_KNOB_4	= MIDICC + $11	; Knob 4	17 ; 0..255
	.equ	MIDI_KNOB_5	= MIDICC + $12	; Knob 5	18 ; 0..255
	.equ	MIDI_KNOB_6	= MIDICC + $13	; Knob 6	19 ; 0..255
	.equ	MIXER_BALANCE	= MIDICC + $14	; Knob 7	20 ; -128..+127
	.equ	MASTER_VOLUME	= MIDICC + $15	; Knob 8	21 ; 0..255

	.equ	ATTACKTIME2	= MIDICC + $16	; Slider 1	22 ; 0..255	 DCF envelope
	.equ	DECAYTIME2	= MIDICC + $17	; Slider 2	23 ; 0..255
	.equ	SUSTAINLEVEL2	= MIDICC + $18	; Slider 3	24 ; 0..255
	.equ	RELEASETIME2	= MIDICC + $19	; Slider 4	25 ; 0..255
	.equ	ATTACKTIME	= MIDICC + $1A	; Slider 5	26 ; 0..255	 DCA envelope
	.equ	DECAYTIME	= MIDICC + $1B	; Slider 6	27 ; 0..255
	.equ	SUSTAINLEVEL	= MIDICC + $1C	; Slider 7	28 ; 0..255
	.equ	RELEASETIME	= MIDICC + $1D	; Slider 8	29 ; 0..255

	.equ	SW1		= MIDICC + $2C ; Reserved	44	required for load a patch from  eeprom
	.equ	SW2		= MIDICC + $2D ; Reserved	45
	.equ	SW3		= MIDICC + $2E ; Reserved	46
	.equ	SW4		= MIDICC + $2F ; Reserved	47

	; Unshifted knobs (potentiometer 0 through 7)
	.equ	RESONANCE	= MIDICC + $30	;		48 ; 0..255
	.equ	CUTOFF		= MIDICC + $31	;		49 ; 0..255
	.equ	LFOFREQ		= MIDICC + $32	;		50 ; 0..255
	.equ	PANEL_LFOLEVEL	= MIDICC + $33	;		51 ; 0..255
	.equ	VCFENVMOD	= MIDICC + $34	;		52 ; -128..+127
	.equ	PORTAMENTO	= MIDICC + $35	;		53 ; 0..255
	.equ	PULSE_KNOB	= MIDICC + $36	; (=LFO2FREQ)	54 ; 0..255
	.equ	OSC_DETUNE	= MIDICC + $37	;		55 ; -128..+127

; Shifted knobs (potentiometer 0 through 7)
;	.equ	X		= MIDICC + $38	; Undefined	56 ; 0..255
;	.equ	X		= MIDICC + $39	; Undefined	57 ; 0..255
	.equ	KNOB_DCF_DECAY	= MIDICC + $3A	;		58 ; 0..255
	.equ	KNOB_DCF_ATTACK	= MIDICC + $3B	;		59 ; 0..255
	.equ	KNOB_AMP_DECAY	= MIDICC + $3C	;		60 ; 0..255
	.equ	KNOB_AMP_ATTACK	= MIDICC + $3D	;		61 ; 0..255
	.equ	ARP_THRESHOLD	= MIDICC + $3E	; 		62 ; 0..255
	.equ	ARP_RATE	= MIDICC + $3F	; 		63 ; 0..255

; Panel switches 0..15
; midi cc switch messages are not stored here
; Switches 2
	.equ	S_KNOB_SHIFT	= MIDICC + $40	;		64
	.equ	S_OSC_FM	= MIDICC + $41	;		65
	.equ	S_LFO_RANDOM	= MIDICC + $42	;		66
	.equ	S_LFO_WAVE	= MIDICC + $43	;		67
	.equ	S_FILTER_MODE	= MIDICC + $44	;		68
	.equ	S_DISTORTION	= MIDICC + $45	;		69
	.equ	S_LFO_ENABLE	= MIDICC + $46	;		70
	.equ	S_LFO_DEST	= MIDICC + $47	;		71
; Switches 1
	.equ	S_ANTI_ALIAS	= MIDICC + $48	;		72
	.equ	S_OSCB_OCT	= MIDICC + $49	;		73
	.equ	S_OSCB_ENABLE	= MIDICC + $4A	;		74
	.equ	S_OSCB_WAVE	= MIDICC + $4B	;		75
	.equ	S_SUSTAIN	= MIDICC + $4C	;		76
	.equ	S_OSCA_NOISE	= MIDICC + $4D	;		77
	.equ	S_PWM_SWEEP	= MIDICC + $4E	;		78
	.equ	S_OSCA_WAVE	= MIDICC + $4F	;		79
; Switches 3
	.equ	S_MIX_RING	= MIDICC + $50	;		80
	.equ	S_VELOCITY	= MIDICC + $51	;		81
	.equ	S_DCA_MODE	= MIDICC + $52	;		84
	.equ	S_DCA_OPEN	= MIDICC + $53	;		82
	.equ	S_TRANSPOSE	= MIDICC + $54	;		83
	.equ	S_MODWHEEL_ENA	= MIDICC + $55	;		85
	.equ	S_LFO_KBD_SYNC	= MIDICC + $56	;		86
	.equ	S_DCF_KBD_TRACK	= MIDICC + $57	;		87
; Switches 4
	.equ	S_USER_4_0	= MIDICC + $58	;		88
	.equ	S_USER_4_1	= MIDICC + $59	;		89
	.equ	S_ARP_ENABLE	= MIDICC + $5A	;		90
	.equ	S_ARP_REPEAT	= MIDICC + $5B	;		91
	.equ	S_USER_4_4	= MIDICC + $5C	;		92
	.equ	S_USER_4_5	= MIDICC + $5D	;		93
	.equ	S_LFO2_WAVE	= MIDICC + $5E	;		94
	.equ	S_LFO2_RANDOM	= MIDICC + $5F	;		95

; Patch save/load and MIDI channel set
LED_STATUS:		.byte	1		; off/on status of front panel LED
LED_TIMER:		.byte	1		; number of blinks before reset
BUTTON_STATUS:		.byte	1		; MIDI=1, SAVE=3, LOAD=7, CLEAR=0
CONTROL_SWITCH:		.byte	1		; Last panel switch moved: 1..16, where zero indicates no movement.
CONTROL_STATE:		.byte	1
	.equ	ENABLE_MIDI_CC_OUT	= 0
	.equ	ENABLE_DEBUG_OUT	= 1

MIDI_TASK_UPDATE:	.byte	1

	.equ	UPDATE_ENV_DCF	= 0
	.equ	UPDATE_ENV_DCA	= 1
	.equ	UPDATE_VOLUME	= 2

.if USE_MASTER_VOLUME
VOLUME:			.byte	1
VOLUME_X4:		.byte	1
.endif	; USE_MASTER_VOLUME

;----------------------------------------------------------------------------

; stack: 0x0A3..0x25F

	.eseg
;					  eeprom addr -> midi cc addr
	.org	0	; default patch

	; Unshifted knobs (potentiometer 0 through 7)
	.db	0x00	; RESONANCE		; $00 -> $30
	.db	0xFE	; CUTOFF		; $01 -> $31
	.db	0x50	; LFOFREQ		; $02 -> $32
	.db	0x80	; PANEL_LFOLEVEL	; $03 -> $33
	.db	0x80	; VCFENVMOD		; $04 -> $34
	.db	0x00	; PORTAMENTO		; $05 -> $35
	.db	0x50	; PULSE_KNOB		; $06 -> $36	; (=LFO2FREQ)
	.db	0x80	; OSC_DETUNE		; $07 -> $37

	; Shifted knobs (potentiometer 0 through 7)
	.db	0	; X			; $08 -> $38 ; Undefined
	.db	0	; X			; $09 -> $39 ; Undefined
	.db	0xA0	; KNOB_DCF_DECAY	; $0A -> $3A
	.db	0x00	; KNOB_DCF_ATTACK	; $0B -> $3B
	.db	0xA0	; KNOB_AMP_DECAY	; $0C -> $3C
	.db	0x00	; KNOB_AMP_ATTACK	; $0D -> $3D
	.db	0	; X			; $0E -> $3E ; Undefined
	.db	0	; X			; $0F -> $3F ; Undefined

	.db	0x50	; LFO2FREQ		; $10 -> $0E	; Knob 1	14
	.db	0x80	; PWMDEPTH		; $11 -> $0F	; Knob 2	15 ; (=LFO2LEVEL)
	.db	0x80	; FMDEPTH		; $12 -> $10	; Knob 3	16
	.db	0x80	; MIDI_KNOB_4		; $13 -> $11	; Knob 4	17 ; currently not used
	.db	0x80	; MIDI_KNOB_5		; $14 -> $12	; Knob 5	18 ; currently not used
	.db	0x80	; MIDI_KNOB_6		; $15 -> $13	; Knob 6	19 ; currently not used
	.db	0x80	; MIXER_BALANCE		; $16 -> $14	; Knob 7	20
	.db	0x80	; MASTER_VOLUME		; $17 -> $15	; Knob 8	21

	.db	0x00	; ATTACKTIME2		; $18 -> $16	; Slider 1	22 ; DCF envelope
	.db	0xFE	; DECAYTIME2		; $19 -> $17	; Slider 2	23
	.db	0xFE	; SUSTAINLEVEL2		; $1A -> $18	; Slider 3	24
	.db	0xA0	; RELEASETIME2		; $1B -> $19	; Slider 4	25
	.db	0x00	; ATTACKTIME		; $1C -> $1A	; Slider 5	26 ; DCA envelope
	.db	0xFE	; DECAYTIME		; $1D -> $1B	; Slider 6	27
	.db	0xFE	; SUSTAINLEVEL		; $1E -> $1C	; Slider 7	28
	.db	0xA0	; RELEASETIME		; $1F -> $1D	; Slider 8	29

	.db	0x00	; SW1 -> PATCH_SWITCH1	; $20 -> $2C
			;	SW_KNOB_SHIFT	= 0	; 0=lower, 1=upper
			;	SW_OSC_FM	= 1	; 0=off, 1=on
			;	SW_LFO_RANDOM	= 2	; 0=norm, 1=rand
			;	SW_LFO_WAVE	= 3	; 0=tri, 1=squ
			;	SW_FILTER_MODE	= 4	; 0=lp, 1=hp
			;	SW_DISTORTION	= 5	; 0=off, 1=on
			;	SW_LFO_ENABLE	= 6	; 0=off, 1=on
			;	SW_LFO_DEST	= 7	; 0=DCF, 1=DCO
	.db	0x15	; SW2 -> PATCH_SWITCH2	; $21 -> $2D
			;	SW_ANTI_ALIAS	= 0 x	; 0=off, 1=on
			;	SW_OSCB_OCT	= 1	; 0=down, 1=up
			;	SW_OSCB_ENABLE	= 2 x	; 0=off, 1=on
			;	SW_OSCB_WAVE	= 3 	; 0=saw, 1=squ
			;	SW_SUSTAIN	= 4 x	; 0=ADR, 1=ASR
			;	SW_OSCA_NOISE	= 5	; 0=off, 1=on
			;	SW_PWM_SWEEP	= 6	; 0=off, 1=LFO2
			;	SW_OSCA_WAVE	= 7 	; 0=saw, 1=squ
	.db	0xF4	; SW3 -> PATCH_SWITCH3	; $22 -> $2E
			;	SW_MIX_RING	= 0	; 0=Mixer(default), 1=Ringmodulator
			;	SW_VELOCITY	= 1	; 0=off, 1=on
			;	SW_DCA_MODE	= 2 x	; 0=gate, 1=env (default)
			;	SW_DCA_OPEN	= 3	; 0=norm, 1=open
			;	SW_TRANSPOSE	= 4 x	; 0=down, 1=up (default)
			;	SW_MODWHEEL_ENA	= 5 x	; 0=diable, 1=enable (default)
			;	SW_LFO_KBD_SYNC	= 6 x	; 0=off, 1=on (default)
			;	SW_DCF_KBD_TRACK= 7 x	; 0=off, 1=on (default)
	.db	0x00	; SW4 -> PATCH_SWITCH4	; $23 -> $2F
			;	SW_USER_4_0	= 0	;
			;	SW_USER_4_1	= 1	;
			;	SW_ARP_ENABLE	= 2	;
			;	SW_ARP_REPEAT	= 3	;
			;	SW_USER_4_4	= 4	;
			;	SW_USER_4_5	= 5	;
			;	SW_LFO2_WAVE	= 6	; 0=tri, 1=squ
			;	SW_LFO2_RANDOM	= 7	; 0=norm, 1=rand

;-------------------------
; second patch

	.org	0x30	; 2nd patch

	; Unshifted knobs (potentiometer 0 through 7)
	.db	0x60	; RESONANCE		; $00 -> $30
	.db	0x80	; CUTOFF		; $01 -> $31
	.db	0x00	; LFOFREQ		; $02 -> $32
	.db	0x00	; PANEL_LFOLEVEL	; $03 -> $33
	.db	0x80	; VCFENVMOD		; $04 -> $34
	.db	0x00	; PORTAMENTO		; $05 -> $35
	.db	0xFE	; PULSE_KNOB		; $06 -> $36	; (=LFO2FREQ)
	.db	0x80	; OSC_DETUNE		; $07 -> $37

	; Shifted knobs (potentiometer 0 through 7)
	.db	0	; X			; $08 -> $38 ; Undefined
	.db	0	; X			; $09 -> $39 ; Undefined
	.db	0x00	; KNOB_DCF_DECAY	; $0A -> $3A
	.db	0x00	; KNOB_DCF_ATTACK	; $0B -> $3B
	.db	0xA0	; KNOB_AMP_DECAY	; $0C -> $3C
	.db	0x00	; KNOB_AMP_ATTACK	; $0D -> $3D
	.db	0	; X			; $0E -> $3E ; Undefined
	.db	0	; X			; $0F -> $3F ; Undefined

	.db	0xFE	; LFO2FREQ		; $10 -> $0E	; Knob 1	14
	.db	0x60	; PWMDEPTH		; $11 -> $0F	; Knob 2	15 ; (=LFO2LEVEL)
	.db	0xFE	; FMDEPTH		; $12 -> $10	; Knob 3	16
	.db	0	; MIDI_KNOB_4		; $13 -> $11	; Knob 4	17 ; currently not used
	.db	0	; MIDI_KNOB_5		; $14 -> $12	; Knob 5	18 ; currently not used
	.db	0	; MIDI_KNOB_6		; $15 -> $13	; Knob 6	19 ; currently not used
	.db	0x80	; MIXER_BALANCE		; $16 -> $14	; Knob 7	20
	.db	0x80	; MASTER_VOLUME		; $17 -> $15	; Knob 8	21

	.db	0x00	; ATTACKTIME2		; $18 -> $16	; Slider 1	22 ; DCF envelope
	.db	0x00	; DECAYTIME2		; $19 -> $17	; Slider 2	23
	.db	0x00	; SUSTAINLEVEL2		; $1A -> $18	; Slider 3	24
	.db	0x00	; RELEASETIME2		; $1B -> $19	; Slider 4	25
	.db	0x00	; ATTACKTIME		; $1C -> $1A	; Slider 5	26 ; DCA envelope
	.db	0xA0	; DECAYTIME		; $1D -> $1B	; Slider 6	27
	.db	0x00	; SUSTAINLEVEL		; $1E -> $1C	; Slider 7	28
	.db	0xA0	; RELEASETIME		; $1F -> $1D	; Slider 8	29

	.db	0x00	; SW1 -> PATCH_SWITCH1	; $20 -> $2C
			;	SW_KNOB_SHIFT	= 0	; 0=lower, 1=upper
			;	SW_OSC_FM	= 1	; 0=off, 1=on
			;	SW_LFO_RANDOM	= 2	; 0=norm, 1=rand
			;	SW_LFO_WAVE	= 3	; 0=tri, 1=squ
			;	SW_FILTER_MODE	= 4	; 0=lp, 1=hp
			;	SW_DISTORTION	= 5	; 0=off, 1=on
			;	SW_LFO_ENABLE	= 6	; 0=off, 1=on
			;	SW_LFO_DEST	= 7	; 0=DCF, 1=DCO
	.db	0x99	; SW2 -> PATCH_SWITCH2	; $21 -> $2D
			;	SW_ANTI_ALIAS	= 0 x	; 0=off, 1=on
			;	SW_OSCB_OCT	= 1	; 0=down, 1=up
			;	SW_OSCB_ENABLE	= 2	; 0=off, 1=on
			;	SW_OSCB_WAVE	= 3 x	; 0=saw, 1=squ
			;	SW_SUSTAIN	= 4 x	; 0=ADR, 1=ASR
			;	SW_OSCA_NOISE	= 5	; 0=off, 1=on
			;	SW_PWM_SWEEP	= 6	; 0=off, 1=LFO2
			;	SW_OSCA_WAVE	= 7 x	; 0=saw, 1=squ
	.db	0xF4	; SW3 -> PATCH_SWITCH3	; $22 -> $2E
			;	SW_MIX_RING	= 0	; 0=Mixer(default), 1=Ringmodulator
			;	SW_VELOCITY	= 1	; 0=off, 1=on
			;	SW_DCA_MODE	= 2 x	; 0=gate, 1=env (default)
			;	SW_DCA_OPEN	= 3	; 0=norm, 1=open
			;	SW_TRANSPOSE	= 4 x	; 0=down, 1=up (default)
			;	SW_MODWHEEL_ENA	= 5 x	; 0=diable, 1=enable (default)
			;	SW_LFO_KBD_SYNC	= 6 x	; 0=off, 1=on (default)
			;	SW_DCF_KBD_TRACK= 7 x	; 0=off, 1=on (default)
	.db	0x00	; SW4 -> PATCH_SWITCH4	; $23 -> $2F
			;	SW_USER_4_0	= 0	;
			;	SW_USER_4_1	= 1	;
			;	SW_ARP_ENABLE	= 2	;
			;	SW_ARP_REPEAT	= 3	;
			;	SW_USER_4_4	= 4	;
			;	SW_USER_4_5	= 5	;
			;	SW_LFO2_WAVE	= 6	; 0=tri, 1=squ
			;	SW_LFO2_RANDOM	= 7	; 0=norm, 1=rand

;-------------------------
; 3rd patch
	.org	0x60	; 3rd patch

	; Unshifted knobs (potentiometer 0 through 7)
	.db	0xFE	; RESONANCE		; $00 -> $30
	.db	0xFE	; CUTOFF		; $01 -> $31
	.db	0xE0	; LFOFREQ		; $02 -> $32
	.db	0x30	; PANEL_LFOLEVEL	; $03 -> $33
	.db	0x00	; VCFENVMOD		; $04 -> $34
	.db	0x00	; PORTAMENTO		; $05 -> $35
	.db	0x28	; PULSE_KNOB		; $06 -> $36	; (=LFO2FREQ)
	.db	0x8E	; OSC_DETUNE		; $07 -> $37

	; Shifted knobs (potentiometer 0 through 7)
	.db	0	; X			; $08 -> $38 ; Undefined
	.db	0	; X			; $09 -> $39 ; Undefined
	.db	0xE8	; KNOB_DCF_DECAY	; $0A -> $3A
	.db	0x00	; KNOB_DCF_ATTACK	; $0B -> $3B
	.db	0x80	; KNOB_AMP_DECAY	; $0C -> $3C
	.db	0x00	; KNOB_AMP_ATTACK	; $0D -> $3D
	.db	0	; X			; $0E -> $3E ; Undefined
	.db	0	; X			; $0F -> $3F ; Undefined

	.db	0x28	; LFO2FREQ		; $10 -> $0E	; Knob 1	14
	.db	0x60	; PWMDEPTH		; $11 -> $0F	; Knob 2	15 ; (=LFO2LEVEL)
	.db	0xFE	; FMDEPTH		; $12 -> $10	; Knob 3	16
	.db	0	; MIDI_KNOB_4		; $13 -> $11	; Knob 4	17 ; currently not used
	.db	0	; MIDI_KNOB_5		; $14 -> $12	; Knob 5	18 ; currently not used
	.db	0	; MIDI_KNOB_6		; $15 -> $13	; Knob 6	19 ; currently not used
	.db	0x80	; MIXER_BALANCE		; $16 -> $14	; Knob 7	20
	.db	0x80	; MASTER_VOLUME		; $17 -> $15	; Knob 8	21

	.db	0x00	; ATTACKTIME2		; $18 -> $16	; Slider 1	22 ; DCF envelope
	.db	0xE8	; DECAYTIME2		; $19 -> $17	; Slider 2	23
	.db	0x00	; SUSTAINLEVEL2		; $1A -> $18	; Slider 3	24
	.db	0xE8	; RELEASETIME2		; $1B -> $19	; Slider 4	25
	.db	0x00	; ATTACKTIME		; $1C -> $1A	; Slider 5	26 ; DCA envelope
	.db	0x80	; DECAYTIME		; $1D -> $1B	; Slider 6	27
	.db	0x00	; SUSTAINLEVEL		; $1E -> $1C	; Slider 7	28
	.db	0x80	; RELEASETIME		; $1F -> $1D	; Slider 8	29

	.db	0x00	; SW1 -> PATCH_SWITCH1	; $20 -> $2C
			;	SW_KNOB_SHIFT	= 0	; 0=lower, 1=upper
			;	SW_OSC_FM	= 1	; 0=off, 1=on
			;	SW_LFO_RANDOM	= 2	; 0=norm, 1=rand
			;	SW_LFO_WAVE	= 3	; 0=tri, 1=squ
			;	SW_FILTER_MODE	= 4	; 0=lp, 1=hp
			;	SW_DISTORTION	= 5	; 0=off, 1=on
			;	SW_LFO_ENABLE	= 6	; 0=off, 1=on
			;	SW_LFO_DEST	= 7	; 0=DCF, 1=DCO
	.db	0x8F	; SW2 -> PATCH_SWITCH2	; $21 -> $2D
			;	SW_ANTI_ALIAS	= 0 x	; 0=off, 1=on
			;	SW_OSCB_OCT	= 1 x	; 0=down, 1=up
			;	SW_OSCB_ENABLE	= 2 x	; 0=off, 1=on
			;	SW_OSCB_WAVE	= 3 x	; 0=saw, 1=squ
			;	SW_SUSTAIN	= 4	; 0=ADR, 1=ASR
			;	SW_OSCA_NOISE	= 5	; 0=off, 1=on
			;	SW_PWM_SWEEP	= 6	; 0=off, 1=LFO2
			;	SW_OSCA_WAVE	= 7 x	; 0=saw, 1=squ
	.db	0xF4	; SW3 -> PATCH_SWITCH3	; $22 -> $2E
			;	SW_MIX_RING	= 0	; 0=Mixer(default), 1=Ringmodulator
			;	SW_VELOCITY	= 1	; 0=off, 1=on
			;	SW_DCA_MODE	= 2 x	; 0=gate, 1=env (default)
			;	SW_DCA_OPEN	= 3	; 0=norm, 1=open
			;	SW_TRANSPOSE	= 4 x	; 0=down, 1=up (default)
			;	SW_MODWHEEL_ENA	= 5 x	; 0=diable, 1=enable (default)
			;	SW_LFO_KBD_SYNC	= 6 x	; 0=off, 1=on (default)
			;	SW_DCF_KBD_TRACK= 7 x	; 0=off, 1=on (default)
	.db	0x00	; SW4 -> PATCH_SWITCH4	; $23 -> $2F
			;	SW_USER_4_0	= 0	;
			;	SW_USER_4_1	= 1	;
			;	SW_ARP_ENABLE	= 2	;
			;	SW_ARP_REPEAT	= 3	;
			;	SW_USER_4_4	= 4	;
			;	SW_USER_4_5	= 5	;
			;	SW_LFO2_WAVE	= 6	; 0=tri, 1=squ
			;	SW_LFO2_RANDOM	= 7	; 0=norm, 1=rand

.if FILL_UP_WITH_DEFAULT_PATCH
;-------------------------
; 4th patch
	.org	0x90	; 4th patch

	.db	0x00, 0xFE, 0x50, 0x80, 0x80, 0x00, 0x50, 0x80
	.db	0,    0,    0xA0, 0x00, 0xA0, 0x00, 0,    0
	.db	0x50, 0x80, 0x80, 0x80, 0x80, 0x80, 0x80, 0x80
	.db	0x00, 0xFE, 0xFE, 0xA0, 0x00, 0xFE, 0xFE, 0xA0
	.db	0x00, 0x15, 0xF4, 0x00

;-------------------------
; 5th patch
	.org	0xC0	; 5th patch

	.db	0x00, 0xFE, 0x50, 0x80, 0x80, 0x00, 0x50, 0x80
	.db	0,    0,    0xA0, 0x00, 0xA0, 0x00, 0,    0
	.db	0x50, 0x80, 0x80, 0x80, 0x80, 0x80, 0x80, 0x80
	.db	0x00, 0xFE, 0xFE, 0xA0, 0x00, 0xFE, 0xFE, 0xA0
	.db	0x00, 0x15, 0xF4, 0x00

;-------------------------
; 6th patch
	.org	0xF0	; 6th patch

	.db	0x00, 0xFE, 0x50, 0x80, 0x80, 0x00, 0x50, 0x80
	.db	0,    0,    0xA0, 0x00, 0xA0, 0x00, 0,    0
	.db	0x50, 0x80, 0x80, 0x80, 0x80, 0x80, 0x80, 0x80
	.db	0x00, 0xFE, 0xFE, 0xA0, 0x00, 0xFE, 0xFE, 0xA0
	.db	0x00, 0x15, 0xF4, 0x00

;-------------------------
; 7th patch
	.org	0x120	; 7th patch

	.db	0x00, 0xFE, 0x50, 0x80, 0x80, 0x00, 0x50, 0x80
	.db	0,    0,    0xA0, 0x00, 0xA0, 0x00, 0,    0
	.db	0x50, 0x80, 0x80, 0x80, 0x80, 0x80, 0x80, 0x80
	.db	0x00, 0xFE, 0xFE, 0xA0, 0x00, 0xFE, 0xFE, 0xA0
	.db	0x00, 0x15, 0xF4, 0x00

;-------------------------
; 8th patch
	.org	0x150	; 8th patch

	.db	0x00, 0xFE, 0x50, 0x80, 0x80, 0x00, 0x50, 0x80
	.db	0,    0,    0xA0, 0x00, 0xA0, 0x00, 0,    0
	.db	0x50, 0x80, 0x80, 0x80, 0x80, 0x80, 0x80, 0x80
	.db	0x00, 0xFE, 0xFE, 0xA0, 0x00, 0xFE, 0xFE, 0xA0
	.db	0x00, 0x15, 0xF4, 0x00

;-------------------------
; 9th patch
	.org	0x180	; 9th patch

	.db	0x00, 0xFE, 0x50, 0x80, 0x80, 0x00, 0x50, 0x80
	.db	0,    0,    0xA0, 0x00, 0xA0, 0x00, 0,    0
	.db	0x50, 0x80, 0x80, 0x80, 0x80, 0x80, 0x80, 0x80
	.db	0x00, 0xFE, 0xFE, 0xA0, 0x00, 0xFE, 0xFE, 0xA0
	.db	0x00, 0x15, 0xF4, 0x00

;-------------------------
; 10th patch
	.org	0x1B0	; 10th patch

	.db	0x00, 0xFE, 0x50, 0x80, 0x80, 0x00, 0x50, 0x80
	.db	0,    0,    0xA0, 0x00, 0xA0, 0x00, 0,    0
	.db	0x50, 0x80, 0x80, 0x80, 0x80, 0x80, 0x80, 0x80
	.db	0x00, 0xFE, 0xFE, 0xA0, 0x00, 0xFE, 0xFE, 0xA0
	.db	0x00, 0x15, 0xF4, 0x00

;-------------------------
; 11th patch
	.org	0x1E0	; 11th patch

	.db	0x00, 0xFE, 0x50, 0x80, 0x80, 0x00, 0x50, 0x80
	.db	0,    0,    0xA0, 0x00, 0xA0, 0x00, 0,    0
	.db	0x50, 0x80, 0x80, 0x80, 0x80, 0x80, 0x80, 0x80
	.db	0x00, 0xFE, 0xFE, 0xA0, 0x00, 0xFE, 0xFE, 0xA0
	.db	0x00, 0x15, 0xF4, 0x00

;-------------------------
; 12th patch
	.org	0x210	; 12th patch

	.db	0x00, 0xFE, 0x50, 0x80, 0x80, 0x00, 0x50, 0x80
	.db	0,    0,    0xA0, 0x00, 0xA0, 0x00, 0,    0
	.db	0x50, 0x80, 0x80, 0x80, 0x80, 0x80, 0x80, 0x80
	.db	0x00, 0xFE, 0xFE, 0xA0, 0x00, 0xFE, 0xFE, 0xA0
	.db	0x00, 0x15, 0xF4, 0x00

;-------------------------
; 13th patch
	.org	0x240	; 13th patch

	.db	0x00, 0xFE, 0x50, 0x80, 0x80, 0x00, 0x50, 0x80
	.db	0,    0,    0xA0, 0x00, 0xA0, 0x00, 0,    0
	.db	0x50, 0x80, 0x80, 0x80, 0x80, 0x80, 0x80, 0x80
	.db	0x00, 0xFE, 0xFE, 0xA0, 0x00, 0xFE, 0xFE, 0xA0
	.db	0x00, 0x15, 0xF4, 0x00

;-------------------------
; 14th patch
	.org	0x270	; 14th patch

	.db	0x00, 0xFE, 0x50, 0x80, 0x80, 0x00, 0x50, 0x80
	.db	0,    0,    0xA0, 0x00, 0xA0, 0x00, 0,    0
	.db	0x50, 0x80, 0x80, 0x80, 0x80, 0x80, 0x80, 0x80
	.db	0x00, 0xFE, 0xFE, 0xA0, 0x00, 0xFE, 0xFE, 0xA0
	.db	0x00, 0x15, 0xF4, 0x00

;-------------------------
; 15th patch
	.org	0x2A0	; 15th patch

	.db	0x00, 0xFE, 0x50, 0x80, 0x80, 0x00, 0x50, 0x80
	.db	0,    0,    0xA0, 0x00, 0xA0, 0x00, 0,    0
	.db	0x50, 0x80, 0x80, 0x80, 0x80, 0x80, 0x80, 0x80
	.db	0x00, 0xFE, 0xFE, 0xA0, 0x00, 0xFE, 0xFE, 0xA0
	.db	0x00, 0x15, 0xF4, 0x00

;-------------------------
; 16th patch
	.org	0x2D0	; 16th patch

	.db	0x00, 0xFE, 0x50, 0x80, 0x80, 0x00, 0x50, 0x80
	.db	0,    0,    0xA0, 0x00, 0xA0, 0x00, 0,    0
	.db	0x50, 0x80, 0x80, 0x80, 0x80, 0x80, 0x80, 0x80
	.db	0x00, 0xFE, 0xFE, 0xA0, 0x00, 0xFE, 0xFE, 0xA0
	.db	0x00, 0x15, 0xF4, 0x00
.endif
;-------------------------

	.org	0x3fe
	.db	0	; current patch
	.db	0	; midi address

;----------------------------------------------------------------------------
;		V E C T O R   T A B L E
;----------------------------------------------------------------------------
	.cseg

	jmp	RESET		; RESET

	jmp	IRQ_NONE	; INT0
	jmp	IRQ_NONE	; INT1
	jmp	IRQ_NONE	; INT2

	jmp	TIM2_CMP	; TIMER2 COMP
	jmp	IRQ_NONE	; TIMER2 OVF

	jmp	IRQ_NONE	; TIMER1 CAPT
	jmp	IRQ_NONE	; TIMER1 COMPA
	jmp	IRQ_NONE	; TIMER1 COMPB
	jmp	IRQ_NONE	; TIMER1 OVF

	jmp	IRQ_NONE	; TIMER0 COMPA
	jmp	IRQ_NONE	; TIMER0 OVF

	jmp	IRQ_NONE	; SPI, STC

	jmp	UART_RXC	; UART, RX COMPLETE
.if USE_SERIAL_OUT
	jmp	UART_UDRE	; UART, UDRE
.else	; USE_SERIAL_OUT
	jmp	IRQ_NONE	; UART, UDRE
.endif	; USE_SERIAL_OUT
	jmp	IRQ_NONE	; UART, TX COMPLETE

	jmp	IRQ_NONE	; ADC CONVERSION COMPLETE

	jmp	IRQ_NONE	; EEPROM READY

	jmp	IRQ_NONE	; ANALOG COMPARATOR

	jmp	IRQ_NONE	; 2-Wire Serial Interface

	jmp	IRQ_NONE	; STORE PROGRAM MEMORY READY

IRQ_NONE:
	reti

;----------------------------------------------------------------------------
;		R O M   T A B L E S
;----------------------------------------------------------------------------
;
; Phase Deltas at 36363.63636 Hz sample rate
;
;		NOTE PHASE DELTA = 2 ^ 24 * Freq / SamplingFreq
;	So...	Note zero calc: 2 ^ 24 * 8.175799 / 36363.63636 = 3772.09651 (stored as 00 0E BC.19)
;
;----------------------------------------------------------------------------

DELTA_C:
	.dw	0xBC19		; \
	.dw	0x000E		; / note  0 ( 8.175799 Hz)
DELTA_CIS:
	.dw	0x9C66		; \
	.dw	0x000F		; / note  1 ( 8.661957 Hz)
DELTA_D:
	.dw	0x8A09		; \
	.dw	0x0010		; / note  2 ( 9.177024 Hz)
DELTA_DIS:
	.dw	0x85CE		; \
	.dw	0x0011		; / note  3 ( 9.722718 Hz)
DELTA_E:
	.dw	0x908B		; \
	.dw	0x0012		; / note  4 (10.300861 Hz)
DELTA_F:
	.dw	0xAB25		; \
	.dw	0x0013		; / note  5 (10.913382 Hz)
DELTA_FIS:
	.dw	0xD68D		; \
	.dw	0x0014		; / note  6 (11.562326 Hz)
DELTA_G:
	.dw	0x13C2		; \
	.dw	0x0016		; / note  7 (12.249857 Hz)
DELTA_GIS:
	.dw	0x63D4		; \
	.dw	0x0017		; / note  8 (12.978272 Hz)
DELTA_A:
	.dw	0xC7E3		; \
	.dw	0x0018		; / note  9 (13.750000 Hz)
DELTA_AIS:
	.dw	0x411D		; \
	.dw	0x001A		; / note 10 (14.567618 Hz)
DELTA_H:
	.dw	0xD0C5		; \
	.dw	0x001B		; / note 11 (15.433853 Hz)
DELTA_C1:
	.dw	0x7831		; \
	.dw	0x001D		; / note 12 (16.351598 Hz)

;----------------------------------------------------------------------------
;
; Lookup Tables
;
; VCF filter cutoff - 128 bytes
; Time to Rate table for calculating amplitude envelopes - 64 bytes
; VCA non-linear level conversion - 256 bytes
;
;----------------------------------------------------------------------------
; VCF Filter Cutoff
;
; caluclated filter coeff, very similar to original values
; value = (16th root of 2)**(index+1)

TAB_VCF:
	.db	  1,   1,   1,   1,   1,   1,   1,   1		;   0
	.db	  1,   2,   2,   2,   2,   2,   2,   2		;   8
	.db	  2,   2,   2,   2,   2,   3,   3,   3		;  16
	.db	  3,   3,   3,   3,   4,   4,   4,   4		;  24
	.db	  4,   4,   5,   5,   5,   5,   5,   6		;  32
	.db	  6,   6,   6,   7,   7,   7,   8,   8		;  40
	.db	  8,   9,   9,  10,  10,  10,  11,  11		;  48
	.db	 12,  12,  13,  13,  14,  15,  15,  16		;  56
	.db	 17,  17,  18,  19,  20,  21,  22,  23		;  64
	.db	 24,  25,  26,  27,  28,  29,  31,  32		;  72
	.db	 33,  35,  36,  38,  40,  41,  43,  45		;  80
	.db	 47,  49,  52,  54,  56,  59,  61,  64		;  88
	.db	 67,  70,  73,  76,  79,  83,  87,  91		;  96
	.db	 95,  99, 103, 108, 112, 117, 123, 128		; 104
	.db	134, 140, 146, 152, 159, 166, 173, 181		; 112
	.db	189, 197, 206, 215, 225, 235, 245, 255		; 120

;----------------------------------------------------------------------------
; Time to Rate conversion table for envelope timing.
; lfo:
;  update values for 32us update rate
;  LFO_INTEGR overflows all 256*32us = 8.192 ms
;
.if !USE_TIMETORATE_64 && !USE_TIMETORATE_128
; formula  Tof = 256*32us*2^16/N
;          LFOfreq = 1/Tof

; Rate value =	Rmin * Q^i with Q = (Rmax/Rmin)^(1/31) = 1,286111766

TIMETORATE:
	;	value		  index	 time
	;	65535		  -	 8,192 ms
	.dw	50957		;  0:	10.54 mS	fast lfo, attack/rise time
	.dw	39621		;  1:	13.55 mS
	.dw	30807		;  2:	17.43 mS
	.dw	23953		;  3:	22.41 mS
	.dw	18625		;  4:	28.83 mS
	.dw	14481		;  5:	37.07 mS
	.dw	11260		;  6:	47.68 mS
	.dw	 8755		;  7:	61.32 mS
	.dw	 6807		;  8:	78.87 mS
	.dw	 5293		;  9:	101.4 mS
	.dw	 4115		; 10:	130.5 mS
	.dw	 3200		; 11:	167.8 mS
	.dw	 2488		; 12:	215.8 mS
	.dw	 1935		; 13:	277.5 mS
	.dw	 1504		; 14:	356.9 mS
	.dw	 1170		; 15:	459.0 mS
	.dw	  909		; 16:	590.4 mS
	.dw	  707		; 17:	759.3 mS
	.dw	  550		; 18:	976.5 mS
	.dw	  427		; 19:	1.256 S
	.dw	  332		; 20:	1.615 S
	.dw	  258		; 21:	2.077 S
	.dw	  201		; 22:	2.672 S
	.dw	  156		; 23:	3.436 S
	.dw	  121		; 24:	4.419 S
	.dw	   94		; 25:	5.684 S
	.dw	   73		; 26:	7.310 S
	.dw	   57		; 27:	9.401 S
	.dw	   44		; 28:	12.09 S
	.dw	   35		; 29:	15.55 S
	.dw	   27		; 20:	20.00 S
	.dw	   19		; 31:	28.26 S	slow lfo, attack/rise time

.else	; !USE_TIMETORATE_64 && !USE_TIMETORATE_128


 .if !USE_TIMETORATE_128
; formula  Tof = 256*32us*2^16/N
;          LFOfreq = 1/Tof

; Rate value =	Rmin * Q^i with Q = (Rmax/Rmin)^(1/63) =

TIMETORATE:
	;	value		  index	 time
	;	65535		  -	  8,192 ms
	.dw	57903		;  0	  9,272 ms	fast lfo, attack/rise time
	.dw	51160		;  1	 10,494 ms
	.dw	45202		;  2	 11,877 ms
	.dw	39938		;  3	 13,442 ms
	.dw	35287		;  4	 15,214 ms
	.dw	31177		;  5	 17,220 ms
	.dw	27547		;  6	 19,489 ms
	.dw	24339		;  7	 22,058 ms
	.dw	21504		;  8	 24,965 ms
	.dw	19000		;  9	 28,256 ms
	.dw	16787		; 10	 31,980 ms
	.dw	14832		; 11	 36,196 ms
	.dw	13105		; 12	 40,966 ms
	.dw	11579		; 13	 46,366 ms
	.dw	10230		; 14	 52,477 ms
	.dw	 9039		; 15	 59,394 ms
	.dw	 7986		; 16	 67,223 ms
	.dw	 7056		; 17	 76,083 ms
	.dw	 6235		; 18	 86,111 ms
	.dw	 5508		; 19	 97,461 ms
	.dw	 4867		; 20	110,307 ms
	.dw	 4300		; 21	124,846 ms
	.dw	 3799		; 22	141,302 ms
	.dw	 3357		; 23	159,926 ms
	.dw	 2966		; 24	181,005 ms
	.dw	 2621		; 25	204,863 ms
	.dw	 2315		; 26	231,865 ms
	.dw	 2046		; 27	262,427 ms
	.dw	 1808		; 28	297,016 ms
	.dw	 1597		; 29	336,165 ms
	.dw	 1411		; 30	380,473 ms
	.dw	 1247		; 31	430,622 ms
	.dw	 1102		; 32	487,380 ms
	.dw	  973		; 33	551,620 ms
	.dw	  860		; 34	624,327 ms
	.dw	  760		; 35	706,617 ms
	.dw	  671		; 36	799,754 ms
	.dw	  593		; 37	905,166 ms
	.dw	  524		; 38	 1,02 s
	.dw	  463		; 39	 1,15 s
	.dw	  409		; 40	 1,31 s
	.dw	  361		; 41	 1,48 s
	.dw	  319		; 42	 1,68 s
	.dw	  282		; 43	 1,90 s
	.dw	  249		; 44	 2,15 s
	.dw	  220		; 45	 2,43 s
	.dw	  195		; 46	 2,75 s
	.dw	  172		; 47	 3,12 s
	.dw	  152		; 48	 3,53 s
	.dw	  134		; 49	 3,99 s
	.dw	  119		; 50	 4,52 s
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
	.db	190, 1,  193, 1,  196, 1,  199, 1,  203, 1,  206, 1,  209, 1,  212, 1	; 104
	.db	215, 1,  218, 1,  222, 1,  225, 1,  228, 1,  232, 1,  235, 1,  238, 1	; 112
	.db	242, 1,  245, 1,  249, 1,  252, 1,  255, 1,  255, 1,  255, 1,  255, 1	; 120

	.db	255, 1,  255, 1,  255, 1,  255, 1,   64, 4,   65, 4,   66, 4,   67, 4	; 128
	.db	 68, 4,   69, 4,   70, 4,   71, 4,   71, 4,   72, 4,   73, 4,   74, 4	; 136
	.db	 75, 4,   76, 4,   77, 4,   78, 4,   80, 4,   81, 4,   82, 4,   83, 4	; 144
	.db	 84, 4,   85, 4,   86, 4,   87, 4,   88, 4,   89, 4,   90, 4,   92, 4	; 152
	.db	 93, 4,   94, 4,   95, 4,   96, 4,   97, 4,   99, 4,  100, 4,  101, 4	; 160
	.db	102, 4,  104, 4,  105, 4,  106, 4,  107, 4,  109, 4,  110, 4,  111, 4	; 168
	.db	113, 4,  114, 4,  115, 4,  117, 4,  118, 4,  119, 4,  121, 4,  122, 4	; 176
	.db	124, 4,  125, 4,  126, 4,  128, 4,  129, 4,  131, 4,  132, 4,  134, 4	; 184
	.db	135, 4,  137, 4,  138, 4,  140, 4,  141, 4,  143, 4,  144, 4,  146, 4	; 192
	.db	148, 4,  149, 4,  151, 4,  153, 4,  154, 4,  156, 4,  157, 4,  159, 4	; 200
	.db	161, 4,  163, 4,  164, 4,  166, 4,  168, 4,  170, 4,  171, 4,  173, 4	; 208
	.db	175, 4,  177, 4,  179, 4,  180, 4,  182, 4,  184, 4,  186, 4,  188, 4	; 216
	.db	190, 4,  192, 4,  194, 4,  196, 4,  198, 4,  199, 4,  201, 4,  203, 4	; 224
	.db	205, 4,  208, 4,  210, 4,  212, 4,  214, 4,  216, 4,  218, 4,  220, 4	; 232
	.db	222, 4,  224, 4,  226, 4,  229, 4,  231, 4,  233, 4,  235, 4,  237, 4	; 240
	.db	240, 4,  242, 4,  244, 4,  246, 4,  249, 4,  251, 4,  253, 4,  255, 4	; 248

;----------------------------------------------------------------------------
;
;----------------------------------------------------------------------------
.endif	; USE_MASTER_VOLUME

;----------------------------------------------------------------------------
;	I N T E R R U P T   S U B R O U T I N E S
;----------------------------------------------------------------------------
; Timer 2 compare interrupt (sampling)
;
; This is where sound is generated. This interrupt is called 36,363 times per second
; to calculate a single 16-bit value for audio output. There are ~440 instruction cycles
; (16MHZ/36,363) between samples, and these have to be shared between this routine and the
; main program loop that scans controls, receives MIDI commands and calculates envelope,
; LFO, and DCA/DCF levels.
;
; If you use too many clock cycles here there won't be sufficient time left over for
; general housekeeping tasks. The result will be sluggish and lost notes, weird timing and sadness.
;----------------------------------------------------------------------------

; Push contents of registers onto the stack
;
	.def	OSC_OUT_L	= r14	; pre-filter audio
	.def	OSC_OUT_H	= r15	; temporary used in ISR, not saved on stack

	.def	LDAC	= r16
	.def	HDAC	= r17
	.def	z_L	= r18
	.def	z_H	= r19
	.def	temp	= r30		; general purpose, used in ISR, saved on stack
	.def	temp2	= r31		; dto

TIM2_CMP:
	push	r16			; wave B
	in	r16, SREG		; \
	push	r16			; / push SREG
	push	r17			; wave A
	push	r18
	push	r19
	push	r20
	push	r21			; PATCH_SWITCH1
	push	r22			; WAVETABLE, PATCH_SWITCH3, temp
	push	r23			; PATCH_SWITCH2
	push	r30			; ZL poiter to tables
	push	r31			; ZH
	push	r0			; MUL result
	push	r1			; dto.

	lds	r21, PATCH_SWITCH1	; Load the mode flag settings so we can check the selected waveform,
	lds	r23, PATCH_SWITCH2	; noise and distortion settings.


;----------------------------------------------------------------------------
;
; Oscillator A & B
;
; This design uses direct frequency synthesis to generate a ramp wave. A three-byte counter (= phase) is being
; incremented by a value which is proportional to the sound frequency (= phase delta). The
; increment takes place every sampling period. The most significant byte of the counter is a sawtooth ramp.
; This is either used as a pointer to a 256 byte wavetable or for direct waveform synthesis.
; Each oscillator has its own phase and phase delta registers. The contents of each phase delta
; register depends on the frequency being generated:
;
;	PHASE DELTA = 2 ^ 24 * Freq / SamplingFreq
;
; where:
;	SamplingFreq = 40000 Hz
;	Freq = 440 * 2 ^ ((n - 69 + d) / 12)
;	where in turn:
;	n = MIDI note number. Range limited to 36 to 96 (5 octaves)
;	d = transpose/detune (in halftones)
;
;----------------------------------------------------------------------------


; Calculate DCO A
					; If Noise switch is on, use pseudo-random shift register value
	sbrs	r23, SW_OSCA_NOISE	; Use noise if bit set, otherwise jump to calculate DCO.
	rjmp	CALC_DCOA
; use galois implementation of LFSR
	lds	r19, LFSR_0		; r16
	lds	r18, LFSR_1		; r17
	lds	r17, LFSR_2		; r18
	bst	r19, 0			; save lsl of LFSR_0

	clc
	ror	r17			; \
	ror	r18			;  > r17:r18:r19 =
	ror	r19			; /  = (LFSR >> 1)

	brtc	NGEN_NOXOR		; test lsb of saved LFSR_0
	ldi	r20, 0xE4		; the taps: b24, b23, b22, b17. This is bit 7, 6, 5 and 0 of the msb.
	eor	r17, r20
NGEN_NOXOR:
	sts	LFSR_0, r19
	sts	LFSR_1, r18
	sts	LFSR_2, r17
	rjmp	CALC_DCOB		; skip sample calc for DCO A if noise bit set

;-------------------------
CALC_DCOA:
	mov	r17, PHASEA_2		; sawtooth ramp for OSCA
	sbrs	r23, SW_OSCA_WAVE	; 0/1 (DCO A = saw/pwm)
	rjmp	DCOA_SAW

; Pulse wave generated by subtracting two bandlimited sawtooths, between 0 and 180 degrees out of phase

	sbrs	r23, SW_PWM_SWEEP
	lds	r20, PULSE_KNOB_LIMITED	; PWM Sweep switch is off, so load the knob value as PWM width
	sbrc	r23, SW_PWM_SWEEP
	lds	r20, PULSE_WIDTH	; PWM Sweep switch is on, load pulse width from LF02
.if USE_ORIGINAL_RAW_OSC
	sbrs	r23, SW_ANTI_ALIAS
	rjmp	RAW_PULSE		; Calculate raw pulse/PWM when anti-alias switch is off
.endif	; USE_ORIGINAL_RAW_OSC
	lds	r22, WAVETABLE_A	; Offset to the correct wavetable, based on note number (0..15)
; r17 phase
; r20 pulse width
; r22 wavetable
	; get sample a into r17
	ldi	ZL, low (2*INV_SAW0)	; Load low part of byte address into ZL
	ldi	ZH, high(2*INV_SAW0)	; Load high part of byte address into ZH
	add	ZL, r17			; Offset the wavetable by the ramp phase (i)
	adc	ZH, r22			; Wavetable 0..15
	lpm				; Load wave(i) into r17

	; get sample b out of phase into r18
	mov	r16, r20		; Grab a copy of the pulse width
	add	r16, r17		; Add phase offset for second table (pulse width + original sample)
	mov	r17, r0			; store previous sample in r17
	ldi	ZL, low (2*INV_SAW0)	; Load low part of byte address into ZL
	ldi	ZH, high(2*INV_SAW0)	; Load high part of byte address into ZH
	add	ZL, r16			; Add phase offset for second table.
	adc	ZH, r22			; Wavetable 0..15
	lpm				; Load wave(i) into r0

	; subtract wave a-b
	; first part b > a, second part b < a
	clr	r16
	sub	r17, r0
	sbc	r16, ZERO
	add	r17, r20		; add offset (pulse width)
	adc	r16, ZERO
	brge	PULSE_BOUND_CHECK	; non-negative result, so no need to limit the value
	ldi	r17, 0
	ldi	r16, 0			; value was negative, so force to zero
PULSE_BOUND_CHECK:
	tst	r16			; Check if we're larger than 255
	breq	PWM_EXIT		; no need to limit upper bound
	ldi	r17, $FF
PWM_EXIT:
	subi	r17, $80		; -128..+127 Sign the sample osc A
	rjmp	CALC_DCOB

.if USE_ORIGINAL_RAW_OSC
; Raw Pulse wave generated on the fly. Aliases like crazy (calc'd only when anti-alias switch is OFF)
RAW_PULSE:
	cp	r17, r20
	brlo	PULSE_ZERO
	ldi	r17, 255
	subi	r17, $80		; -128..+127 Sign the sample osc A
	rjmp	CALC_DCOB
PULSE_ZERO:
	ldi	r17, 0
	subi	r17, $80		; -128..+127 Sign the sample osc A
	rjmp	CALC_DCOB
.endif	; USE_ORIGINAL_RAW_OSC

; Calculate DCOA sawtooth
DCOA_SAW:
.if USE_ORIGINAL_RAW_OSC
	mov	r17, PHASEA_2
	sbrs	r23, SW_ANTI_ALIAS
	rjmp	DCOA_SAW_SIGN
.endif	; USE_ORIGINAL_RAW_OSC

	lds	r22, WAVETABLE_A	; Offset to the correct wavetable, based on note number (0..15)
	ldi	ZL, low(2*INV_SAW0)	; Load low part of byte address into ZL
	ldi	ZH, high(2*INV_SAW0)	; Load high part of byte address into ZH
	add	ZL, r17			; Offset the wavetable by the ramp phase (i)
	adc	ZH, r22			; Wavetable 0..15
	lpm	r17, z
DCOA_SAW_SIGN:
	subi	r17, $80		; -128..+127 Sign the sample osc B
; r17 hold DCO A waveform

;----------------------------------------------------------------------------
; Calculate DCO B
CALC_DCOB:
	lds	r22, WAVETABLE_B	; Offset to the correct wavetable, based on note number (0..15)
.if USE_ORIGINAL_RAW_OSC
	sbrs	r23, SW_ANTI_ALIAS
	ldi	r22, 0			; Use wavetable 0 when anti-alias switch off
.endif	; USE_ORIGINAL_RAW_OSC
	mov	r16, PHASEB_2		; Use ramp value as offset when scanning wavetable
	sbrs	r23, SW_OSCB_WAVE	; 0/1 (DCO B = saw/squ)
	rjmp	LIMITED_TRIB

LIMITED_SQB:				; Square wave lookup
	ldi	ZL, low(2*SQ_LIMIT0)	; Load low part of byte address into ZL
	ldi	ZH, high(2*SQ_LIMIT0)	; Load high part of byte address into ZH
	add	ZL, r16			; Offset the wavetable by the ramp phase (i)
	adc	ZH, r22			; Wavetable 0..15
	lpm	r16, z
	rjmp	CALC_DIST

LIMITED_TRIB:				; Triangle wave lookup
	ldi	ZL, low(2*TRI_LIMIT0)	; Load low part of byte address into ZL
	ldi	ZH, high(2*TRI_LIMIT0)	; Load high part of byte address into ZH
	add	ZL, r16			; Offset the wavetable by the ramp phase (i)
	adc	ZH, r22			; Wavetable 0..15
	lpm	r16, z
; r16 hold DCO B waveform

CALC_DIST:
	subi	r16, $80		; -128..+127 Sign the sample osc B

	sbrc	r21, SW_DISTORTION	; 0/1 (OSC DIST = off/on)
	eor	r17, r16

					; Turn off OSCB if not enabled
;	sbrs	r23, SW_OSCB_ENABLE
;	ldi	r16, 0

;----------------------------------------------------------------------------
; Sum Oscillators
;
; Combines DCOA (in r17) and DCOB (in r16) waves to produce a 16-bit signed result in HDAC:LDAC (r17:r16)
;
;----------------------------------------------------------------------------

.if USE_ORIGINAL_DCO_FM
	sts	WAVEB, r16		; store signed DCO B wave for fm
.endif	; USE_ORIGINAL_DCO_FM

.if USE_RINGMODULATOR
	lds	r22, PATCH_SWITCH3
	sbrc	r22, SW_MIX_RING
	rjmp	RINGMOD
.endif	; USE_RINGMODULATOR

; mixer:
; Mixer out = (A*x + B*(1-x))/4   x=0..1
	lds	r22, DCOA_LEVEL		; x=0..254/256
	mulsu	r17, r22		; signed DCO A wave * level
	movw	temp, r0		; store value in temp register
	lds	r22, DCOB_LEVEL		; (1-x)=254/256..0
	sbrs	r23, SW_OSCB_ENABLE	; if OSC B disabled add OSC A twice
	mov	r16, r17		; (A*x + A*(1-x))/4   x=0..1
	mulsu	r16, r22		; signed DCO B wave * level
	add	temp, r0
	adc	temp2, r1		; sum scaled waves
	movw	r16, temp		; place signed output in HDAC:LDAC

	; rotate right a couple of times to make a couple of bits of headroom for resonance.
	asr	r17			; \
	ror	r16			; / r17:r16 = r17:r16 asr 1
.if USE_ORIGINAL_MIXER_LEVEL
	asr	r17			; \
	ror	r16			; / r17:r16 = r17:r16 asr 1
.endif	; USE_ORIGINAL_MIXER_LEVEL
.if USE_RINGMODULATOR
	rjmp	MIXER_END

;----------------------------------------------------------------------------
; Ringmodulator
;----------------------------------------------------------------------------
; multiply DCO A (in r17) with DCO B (in r16) output
; skips mixer

RINGMOD:
.if USE_RINGMODULATOR_BALANCE
; (A*x * B*(1-x))/4   x=0..1
; ABx - ABxx = ABx * (1-x)	outpult level max. A*B/4
;
	lds	r22, DCOA_LEVEL		; x=0..254/256
	mulsu	r17, r22		; signed DCO A wave * level
	mov	r17, r1
	lds	r22, DCOB_LEVEL		; (1-x)=254/256..0
	mulsu	r16, r22		; signed DCO B wave * level
	mov	r16, r1
.endif	; USE_RINGMODULATOR_BALANCE

; ring moudulator out = (A*B) or (A*B)/4
	muls	r17, r16		; modulation

.if USE_ORIGINAL_DCO_FM
	sts	WAVEB, r16		; store signed DCO B wave for fm
.endif	; USE_ORIGINAL_DCO_FM
	movw	r16, r0			; place signed output in HDAC:LDAC

.if USE_ORIGINAL_MIXER_LEVEL
.if USE_RINGMODULATOR_BALANCE
	lsl	r16			; increase ringmodulator output +6db
	rol	r17
.else	; USE_RINGMODULATOR_BALANCE
	; rotate right a couple of times to make a couple of bits of headroom for resonance.
	asr	r17			; \
	ror	r16			; / r17:r16 = r17:r16 asr 1
.endif	; USE_RINGMODULATOR_BALANCE
.endif	; USE_ORIGINAL_MIXER_LEVEL

MIXER_END:
.endif	; USE_RINGMODULATOR
	movw	OSC_OUT_L, r16		; keep a copy for highpass filter

;----------------------------------------------------------------------------
; DCF:
;----------------------------------------------------------------------------

;----------------------------------------------------------------------------
; Digitally Controlled Filter
;
; A 2-pole resonant low pass filter:
;
; a += f * ((in - a) + q * 4 * (a - b))
; b += f * (a - b)
;
; f = (1-F)/2+Q_offset
; q = Q-f = Q-(1-F)/2+Q_offset
;
; F = LPF (cutoff)
; Q = RESONANCE
; q = SCALED_RESONANCE
; b => output
;
; Input 16-Bit signed HDAC:LDAC (r17:r16), already scaled to minimize clipping (reduced to 25% of full code).
;
;----------------------------------------------------------------------------
; see also
;   http://www.kvraudio.com/forum/printview.php?t=225711
;----------------------------------------------------------------------------

	; calc (in - a) ; both signed
	sub	LDAC, a_L
	sbc	HDAC, a_H
					; check for overflow / do hard clipping
	brvc	OVERFLOW_1		; if overflow bit is clear jump to OVERFLOW_1
					; sub overflow happened -> set to min
					; 0b1000.0000 0b0000.0001 -> min
					; 0b0111.1111 0b1111.1111 -> max
	ldi	LDAC, 0b00000001
	ldi	HDAC, 0b10000000
OVERFLOW_1:				; when overflow is clear

					; (in-a) is now in HDAC:LDAC as signed
					; now calc q*(a-b)
	lds	r22, SCALED_RESONANCE	; load filter Q value, unsigned
OVERFLOW_2:

	mov	r20, a_L		; \
	mov	r21, a_H		; / load 'a' , signed
	lds	z_H, b_H		; \
	lds	z_L, b_L		; / load 'b', signed
	sub	r20, z_L		; \
	sbc	r21, z_H		; / (a-b) signed
	brvc	OVERFLOW_3		; if overflow is clear jump to OVERFLOW_3
					; 0b1000.0000 0b0000.0001 -> min
					; 0b0111.1111 0b1111.1111 -> max
	ldi	r20, 0b00000001
	ldi	r21, 0b10000000
OVERFLOW_3:

	lds	r18, PATCH_SWITCH1	; Check Low Pass/High Pass panel switch.
	sbrs	r18, SW_FILTER_MODE
	rjmp	CALC_LOWPASS

SKIP_REZ:
	movw	z_L, r20		; High Pass selected, so just load r21:r20 into z_H:z_L to disable Q
	rjmp	DCF_ADD			; Skip lowpass calc

CALC_LOWPASS:
	; skip resonance calculation if VCF is turned off (value of 0)
	lds	r18, VCF_STATUS
	tst	r18			; test for ENV_STOP
	breq	SKIP_REZ
					; mul signed:unsigned -> (a-b) * q
					; 16x8 into 16-bit
					; r19:r18 = r21:r20 (ah:al) * r22 (b)
	mulsu	r21, r22		; (signed)ah * b
	movw	r18, r0
	mul	r20, r22		; al * b
	add	r18, r1
	adc	r19, ZERO
	rol	r0			; r0.7 --> Cy
	brcc	NO_ROUND		; LSByte < $80, so don't round up
	inc	r18
NO_ROUND:
	clc				; (a-b) * q * 4
	lsl	r18
	rol	r19
OVERFLOW_3A:
	clc
	lsl	r18
	rol	r19
OVERFLOW_3B:

	movw	z_L, r18		; q*(a-b) in z_H:z_L as signed
					; add both
					; both signed
					; ((in-a)+q*(a-b))
					; => HDAC:LDAC + z_H:z_L
DCF_ADD:
	add	LDAC, z_L
	adc	HDAC, z_H

	brvc	OVERFLOW_4		; if overflow is clear
					; 0b1000.0000 0b0000.0001 -> min
					; 0b0111.1111 0b1111.1111 -> max
	ldi	LDAC, 0b11111111
	ldi	HDAC, 0b01111111
OVERFLOW_4:
					; Result is a signed value in HDAC:LDAC
					; calc * f
					; ((in-a)+q*(a-b))*f
	lds	r20, LPF_I		; load lowpass 'F' value
	lds	r18, PATCH_SWITCH1
	sbrc	r18, SW_FILTER_MODE	; Check LP/HP switch.
	lds	r20, HPF_I		; Switch set, so load 'F' for HP
					; mul signed unsigned HDAC*F
					; 16x8 into 16-bit
					; r19:r18 = HDAC:LDAC (ah:al) * r20 (b)
	mulsu	HDAC, r20		; (signed)ah * b
	movw	r18, r0
	mul	LDAC, r20		; al * b
	add	r18, r1			; signed result in r19:r18
	adc	r19, ZERO
	rol	r0			; r0.7 --> Cy
	brcc	NO_ROUND2		; LSByte < $80, so don't round up
	inc	r18
NO_ROUND2:
					; Add result to 'a'
					; a+=f*((in-a)+q*(a-b))
	add	a_L, r18
	adc	a_H, r19
	brvc	OVERFLOW_5		; if overflow is clear
					; 0b1000.0000 0b0000.0001 -> min
					; 0b0111.1111 0b1111.1111 -> max
	ldi	z_L, 0b11111111
	ldi	z_H, 0b01111111
	mov	a_L, z_L
	mov	a_H, z_H
OVERFLOW_5:
					; calculated a+=f*((in-a)+q*(a-b)) as signed value and saved in a_H:a_L
					; calc 'b'
					; b += f * (a*0.5 - b)
	mov	z_H, a_H		; \
	mov	z_L, a_L		; / load 'a' as signed

	lds	temp, b_L		; \
	lds	temp2, b_H		; / load b as signed

	sub	z_L, temp		; \
	sbc	z_H, temp2		; / (a - b) signed

	brvc	OVERFLOW_6		; if overflow is clear
					; 0b1000.0000 0b0000.0001 -> min
					; 0b0111.1111 0b1111.1111 -> max
	ldi	z_L, 0b00000001
	ldi	z_H, 0b10000000
OVERFLOW_6:

	lds	r20, LPF_I		; load lowpass 'F' value
	lds	r18, PATCH_SWITCH1
	sbrc	r18, SW_FILTER_MODE	; Check LP/HP switch.
	lds	r20, HPF_I		; Switch set to HP, so load 'F' for HP
					; mul signed unsigned (a-b) * F
					; 16x8 into 16-bit
					; r19:r18 = z_H:z_L (ah:al) * r20 (b)
	mulsu	z_H, r20		; (signed)ah * b
	movw	r18, r0
	mul	z_L, r20		; al * b
	add	r18, r1			; signed result in r19:r18
	adc	r19, ZERO

	add	temp,  r18		; \ add result to 'b' , signed
	adc	temp2, r19		; / b +=(a-b)*f

	brvc	OVERFLOW_7		; if overflow is clear
					; 0b1000.0000 0b0000.0001 -> min
					; 0b0111.1111 0b1111.1111 -> max
	ldi	temp,  0b11111111
	ldi	temp2, 0b01111111
OVERFLOW_7:

	sts	b_L, temp		; \
	sts	b_H, temp2		; / save value of 'b'
	mov	LDAC, temp		; B now contains the filtered signal in HDAC:LDAC
	mov	HDAC, temp2		; output sample HDAC:LDAC = r17:r16

					; If in HP filter mode, just use (filter input - filter output)
	lds	r18, PATCH_SWITCH1	; Check if LP or HP filter
	sbrs	r18, SW_FILTER_MODE
	rjmp	DCA			; LP, so jump to DCA
	sub	OSC_OUT_L, LDAC		; HP filter, so output = filter input - output
	sbc	OSC_OUT_H, HDAC
	movw	LDAC, OSC_OUT_L		; output sample HDAC:LDAC = r17:r16

;----------------------------------------------------------------------------
; Digitally Controlled Amplifier
;
; Multiply the output waveform by the 8-bit value in LEVEL.
; r17:r16 - output from filter 16b signed
; r18     - output from DCA envelope generator
;----------------------------------------------------------------------------
;
DCA:
	movw	r30, r16
	lds	r18, LEVEL
	cpi	r18, 255
	breq	T2_AEXIT		; don't multiply when LEVEL==255, use
	mulsu	r17, r18		; multiply samples high byte
	movw	r30, r0
	mul	r16, r18		; multipliy samples low byte
	add	r30, r1
	adc	r31, ZERO
T2_AEXIT:

.if USE_MASTER_VOLUME
; r31:30, r0  sample
; r18	  volume +12db..-36db (255..0), 0db = 64
	lds	r18, VOLUME_X4
	cpi	r18, 4
	brne	VOL_AEXIT		; don't multiply when VOLUME = 0x40 (0db), use

	lsl	r0			; multiply by 4
	rol	r30
	rol	r31
	lsl	r0
	rol	r30
	rol	r31
VOL_AEXIT:
.endif	; USE_MASTER_VOLUME

;----------------------------------------------------------------------------
; Output Sample
;
; Write the 16-bit signed output of the DCA to the DAC.
;----------------------------------------------------------------------------

; write sample (r31:r30) to DAC:
	sbi	PORTD, DAC_WR		; Set WR high
	subi	r31, 128		; U2 --> PB
	cbi	PORTD, DAC_AB		; Select DAC port A
	out	PORTC, r31		; output most significant byte
	cbi	PORTD, DAC_WR		; Pull WR low to load buffer A
	sbi	PORTD, DAC_WR		; Set WR high
	sbi	PORTD, DAC_AB		; Select DAC port B
	out	PORTC, r30		; output least significant byte
	cbi	PORTD, DAC_WR		; Pull WR low to load buffer B
	sbi	PORTD, DAC_WR		; Set WR high again

; Increment Oscillator A & B phase
	ldi	r30, low(DELTAA_0)
	ldi	r31, high(DELTAA_0)
	ld	r16, z+
	add	PHASEA_0, r16
	ld	r16, z+
	adc	PHASEA_1, r16
	ld	r16, z+
	adc	PHASEA_2, r16
	ld	r16, z+
	add	PHASEB_0, r16
	ld	r16, z+
	adc	PHASEB_1, r16
	ld	r16, z+
	adc	PHASEB_2, r16

;----------------------------------------------------------------------------
; Frequency Modulation
;----------------------------------------------------------------------------
;
.if USE_ORIGINAL_DCO_FM
DCO_FM:

	lds	r30, PATCH_SWITCH2
	sbrc	r30, SW_OSCA_NOISE
	rjmp	END_SAMPLE_LOOP		; If DCOA waveform is set to Noise, skip FM

	sbrs	r30, SW_OSCB_ENABLE	; Skip FM is OSCB is turned off
	rjmp	END_SAMPLE_LOOP

	lds	r30, PATCH_SWITCH1	; Get FM switch value
	sbrs	r30, SW_OSC_FM
	ldi	r17, 0			; Set FM depth to 0 if switch is off
	sbrc	r30, SW_OSC_FM
.if !USE_MIDI_FMDEPTH
	ldi	r17, 255		; Set FM depth to 255 if switch is on
.else	; !USE_MIDI_FMDEPTH
	lds	r17, FMDEPTH
.endif	; !USE_MIDI_FMDEPTH
					; mod * depth
	tst	r17			; skip if FM depth is zero
	breq	END_SAMPLE_LOOP
	lds	r16, WAVEB

	mulsu	r16, r17		; mod(=waveb) * depth -> r19:r18
	movw	r18, r0

					; delta * mod * depth
	lds	r16, DELTAA_0
	clr	r17
	mulsu	r19, r16
	sbc	r17, r17		; sign extension
	add	PHASEA_0, r1
	adc	PHASEA_1, r17
	adc	PHASEA_2, r17

	lds	r16, DELTAA_1
	mulsu	r19, r16
	add	PHASEA_0, r0
	adc	PHASEA_1, r1
	adc	PHASEA_2, r17

	lds	r16, DELTAA_2
	mulsu	r19, r16
	add	PHASEA_1, r0
	adc	PHASEA_2, r1
.endif	; USE_ORIGINAL_DCO_FM

;----------------------------------------------------------------------------
; End of Sample Interrupt
;
; Pop register values off stack and return to our regularly scheduled programming.
;----------------------------------------------------------------------------

END_SAMPLE_LOOP:

	pop	r1
	pop	r0
	pop	r31
	pop	r30
	pop	r23
	pop	r22
	pop	r21
	pop	r20
	pop	r19
	pop	r18
	pop	r17
	pop	r16			; \
	out	SREG, r16		; / pop SREG
	pop	r16
	reti

	.undef	OSC_OUT_L		; r14 pre-filter audio
	.undef	OSC_OUT_H		; r15 temporary used in ISR, not saved on stack
	.undef	LDAC			; r16
	.undef	HDAC			; r17
	.undef	z_L			; r18
	.undef	z_H			; r19

	.undef	temp			; r30 general purpose, used in ISR, saved on stack
	.undef	temp2			; r31 dto

;----------------------------------------------------------------------------
; UART receiver (MIDI IN)
;----------------------------------------------------------------------------
UART_RXC:

	push	r16
	in	r16, SREG		; \
	push	r16			; / push SREG

	in	r16, UDR		; read received byte in r16
	cbi	UCSRB, RXCIE		; RXCIE=0 (disable UART interrupts)
	sei				; enable other interrupts
	push	r17

	tst	r16			; \ jump when
	brpl	INTRX_DATA		; / r16.7 == 0 (MIDI data byte)

; MIDI status byte (1xxxxxxx) in r16:
	mov	r17, r16
	andi	r17, 0xF0
	cpi	r17, 0x80
	breq	INTRX_ACCEPT		; 8x note off
	cpi	r17, 0x90
	breq	INTRX_ACCEPT		; 9x note on
	cpi	r17, 0xB0
	breq	INTRX_ACCEPT		; Bx control change
	cpi	r17, 0xE0
	breq	INTRX_ACCEPT		; Ex pitch bend
	ldi	r17, 0			; \
	sts	MIDIPHASE, r17		; / MIDIPHASE = 0
	rjmp	INTRX_EXIT		; Ax polyphonic aftertouch
					; Cx program change
					; Dx channel aftertouch
					; Fx system

INTRX_ACCEPT:
	sts	MIDIPHASE, r17		; phase = 80 90 B0 E0
	andi	r16, 0x0F		; \
	inc	r16			;  > store MIDI channel 1..16
	sts	MIDICHANNEL, r16	; /
	lds	r17, SETMIDICHANNEL	; 0 for OMNI or 1..15
	tst	r17
	breq	INTRX_ACPT_X		; end when OMNI
	cp	r17, r16		; compare set channel to the incoming channel
	breq	INTRX_ACPT_X		; end when right channel
	ldi	r17, 0			; \ otherwise:
	sts	MIDIPHASE, r17		; / MIDIPHASE = 0 (no data service)

INTRX_ACPT_X:
	rjmp	INTRX_EXIT

; MIDI data byte (0xxxxxxx) in r16:
INTRX_DATA:
	lds	r17, MIDIPHASE
;----------------------------------------------------------------------------
; 8x note off:
	cpi	r17, 0x80		; \
	breq	INTRX_NOFF1		;  \
	cpi	r17, 0x81		;  / note off
	breq	INTRX_NOFF2		; /
	rjmp	INTRX_NOTEON

INTRX_NOFF1:
	inc	r17			; \
	sts	MIDIPHASE, r17		; / MIDIPHASE = 0x81
	sts	MIDIDATA0, r16		;   MIDIDATA0 = d
	rjmp	INTRX_EXIT

INTRX_NOFF2:
	dec	r17			; \
	sts	MIDIPHASE, r17		; / MIDIPHASE = 0x80
	rjmp	INTRXNON2_OFF

;----------------------------------------------------------------------------
; 9x note on:
INTRX_NOTEON:
	cpi	r17, 0x90		; \
	breq	INTRX_NON1		;  \
	cpi	r17, 0x91		;  / note on
	breq	INTRX_NON2		; /
	rjmp	INTRX_CTRL

INTRX_NON1:
	inc	r17			; \
	sts	MIDIPHASE, r17		; / MIDIPHASE = 0x91
	sts	MIDIDATA0, r16		;   MIDIDATA0 = note
	rjmp	INTRX_EXIT

INTRX_NON2:
	dec	r17			; \
	sts	MIDIPHASE, r17		; / MIDIPHASE = 0x90
	tst	r16			; \ MIDIDATA0 = velocity
	brne	INTRXNON2_ON		; / jump when velocity != 0

; turn note off:
INTRXNON2_OFF:
	lds	r16, MIDIDATA0		; new note
;-------------------------
.if !USE_ARPEGGIATOR
	lds	r17, MIDINOTEPREV
	cp	r16, r17		; same note as previous note
	brne	INTRXNON2_OFF1		; no
	ldi	r17, 255		; \ yes: remove previous note
	sts	MIDINOTEPREV, r17	; / from buffer

INTRXNON2_OFF1:
	lds	r17, MIDINOTE		; current note
	cp	r16, r17		; \
	brne	INTRXNON2_OFF3		; / exit when not the same note
	lds	r17, MIDINOTEPREV
	cpi	r17, 255		; previous note is invalid?
	breq	INTRXNON2_OFF2		; yes: no more notes => gate = 0
	sts	MIDINOTE, r17		; previous note is now valid again
	ldi	r17, 255		; \ remove previous note
	sts	MIDINOTEPREV, r17	; / from buffer

INTRXNON2_OFF3:
	rjmp	INTRX_EXIT

INTRXNON2_OFF2:
	ldi	r17, 255		; \
	sts	MIDINOTE, r17		; / remove last note
;-------------------------
.else	; !USE_ARPEGGIATOR
	rcall	note_delete		; remove note (r16) from buffer
	rcall	note_current		; get the next valid note from the buffer
	sts	MIDINOTE_NEXT, r16	; update MIDINOTE, can be invalid
	cpi	r16, 255
	breq	INTRXNON2_OFF4		; no more notes => gate = 0
	rjmp	INTRX_EXIT
INTRXNON2_OFF4:
.endif	; !USE_ARPEGGIATOR

	ldi	r17, 0			; \
	sts	GATE, r17		; / GATE = 0

	sbi	PORT_MIDI_LED, MIDI_LED	; LED on
	rjmp	INTRX_EXIT

; turn note on:
INTRXNON2_ON:
	sts	MIDIVELOCITY, r16	; store velocity
					; use velocity of last pessed note
;-------------------------
.if !USE_ARPEGGIATOR
	lds	r17, MIDINOTE		; \ move previous note
	sts	MIDINOTEPREV, r17	; / into buffer
	lds	r17, MIDIDATA0		; \
	sts	MIDINOTE, r17		; / MIDINOTE = note#
;-------------------------
.else	; !USE_ARPEGGIATOR
	lds	r16, MIDIDATA0
	rcall	note_add		; store the note in the next free location in the buffer
	rcall	note_current		; get the next valid note from the buffer
	sts	MIDINOTE_NEXT, r16	; update MIDINOTE, can be invalid
.endif	; !USE_ARPEGGIATOR

	ldi	r17, 1			; \
	sts	GATE, r17		; / GATE = 1
	sts	GATEEDGE, r17		; GATEEDGE = 1

	cbi	PORT_MIDI_LED, MIDI_LED	; LED off
	rjmp	INTRX_EXIT

;----------------------------------------------------------------------------
; Bx control change:
INTRX_CTRL:
	cpi	r17, 0xB0		; \
	breq	INTRX_CC1		;  \
	cpi	r17, 0xB1		;  / control change
	breq	INTRX_CC2		; /
	rjmp	INTRX_PBEND

INTRX_CC1:
; controller number in r16
	inc	r17			; \
	sts	MIDIPHASE, r17		; / MIDIPHASE = 0xB1
	sts	MIDIDATA0, r16		;   MIDIDATA0 = controller#
	rjmp	INTRX_EXIT

INTRX_CC2:
; parameter value in r16
	dec	r17			; \
	sts	MIDIPHASE, r17		; / MIDIPHASE = 0xB0
	lds	r17, MIDIDATA0		;   controller #

; Store MIDI CC in table
	push	r26			; store contents of r27 and r26 on stack
	push	r27

	cpi	r17, $30		; Just save a controller # < $30, also the unsupported controllers
	brlo	INTRX_GOSAVE

	cpi	r17, $40		; save, update old knob value and status
	brlo	INTRX_KNOB

	cpi	r17, $50		; save, update old switch value and status
	brlo	INTRX_SW

	cpi	r17, $60		; for addional switches  (PATCHSWITCH3, PATCH_SWITCH4)
	brlo	INTRX_GOSW_EXT

INTRX_GOSAVE:
	rjmp	INTRX_SAVE		; Save all other controllers

INTRX_GOSW_EXT:
	rjmp	INTRX_SW_EXT

; - - - - - - - - - - - - - - - - - - - - - - - - - - - - - - - - - - - - - -

INTRX_KNOB:
	; save the value in the MIDI table
	ldi	r26, low(MIDICC)
	ldi	r27, high(MIDICC)
	add	r26, r17		; r17 controller index, r16 MIDI data
	adc	r27, zero
	lsl	r16			; shift MIDI data to 0..254 to match knob value
	st	x, r16			; store in MIDI CC table
; when MIDI data (r16) is greater zero, overwrite ADSR and other alternative parameters
	breq	INTRX_KNOB_ADC

; for midi controller CC54 do a special processing
	cpi	r17, $36	 	; CC54 Knob PULSE_KNOB
	breq	INTRX_PULSE_KNOB	; CC54 -> update LFO 2 frequeny

; for  midi controllers CC58..CC61 do a special processing
	cpi	r17, $3A	 	; CC58 Knob FLT_DECAY
	brlo	INTRX_KNOB_ADC
	breq	INTRX_KNOB_DCF_DECAY	; CC58 -> update filter decay time
	cpi	r17, $3C		; CC60 Knob AMP_DECAY
	brlo	INTRX_KNOB_DCF_ATTACK	; CC59 -> update filter attack time
	breq	INTRX_KNOB_AMP_DECAY	; CC60 -> update amplifier decay time
	cpi	r17, $3E		; CC62
	brcc	INTRX_KNOB_ADC
					; CC61 -> update amplifier attack time
INTRX_KNOB_AMP_ATTACK:
	sts	ATTACKTIME, r16		; sync with KNOB_AMP_ATTACK
	rjmp	INTRX_KNOB_ADC

INTRX_KNOB_AMP_DECAY:			; update amplifier decay time
	; set update_env_dca flags
	lds	r26, MIDI_TASK_UPDATE
	ori	r26, (1<<UPDATE_ENV_DCA)
	sts	MIDI_TASK_UPDATE, r26
	rjmp	INTRX_KNOB_ADC

INTRX_KNOB_DCF_ATTACK:
	sts	ATTACKTIME2, r16	; sync with KNOB_DCF_ATTACK
	rjmp	INTRX_KNOB_ADC

INTRX_KNOB_DCF_DECAY:
	; set update_env_dcf flags
	lds	r26, MIDI_TASK_UPDATE
	ori	r26, (1<<UPDATE_ENV_DCF)
	sts	MIDI_TASK_UPDATE, r26
	rjmp	INTRX_KNOB_ADC

INTRX_PULSE_KNOB:
	sts	LFO2FREQ, r16		; sync with PULSE_KNOB

INTRX_KNOB_ADC:
					; Get ADC_X and write it into OLD_ADC_X
	subi	r17, $30		; reduce to 0..15
	cbr	r17, $f8		; Clear highest 5 bits, leaving knob 0..7

	ldi	r26, low(ADC_0)		; get current adc value
	ldi	r27, high(ADC_0)
	add	r26, r17
	adc	r27, zero
	ld	r16, x			; Fetch ADC_X into r16

	ldi	r26, low(OLD_ADC_0)	; update old adc value with current adc value
	ldi	r27, high(OLD_ADC_0)
	add	r26, r17
	adc	r27, zero
	st	x, r16			; Store ADC_X in OLD_ADC_X

	; Clear KNOBX_STATUS (knob not moved)
	ldi	r26, low(KNOB0_STATUS)
	ldi	r27, high(KNOB0_STATUS)
	add	r26, r17
	adc	r27, zero
	ldi	r17, 0
	st	x, r17			; Clear KNOBX_STATUS
	rjmp	INTRX_CCEND

; - - - - - - - - - - - - - - - - - - - - - - - - - - - - - - - - - - - - - -

INTRX_SW:
	subi	r17, $40		; MIDI CC # --> switch offset 0..15
	cpi	r17, $08
	BRLO	INTRX_SWITCH1		; Jump to Switch 1 if switch 0..7 selected.

INTRX_SWITCH2:
; r16 parameter value = switch state: 0..63=off, 64..127=on
; r17 contoller# = switch
	cbr	r17, $f8		; Clear highest 5 bits, leaving switch 0..7
	lds	r26, PATCH_SWITCH2
	bst	r16, 6			; load MSB of MIDI CC value into SREG T bit
	cpi	r17, 0
	brne	INTRX_S1
	bld	r26, SW_ANTI_ALIAS	; Set bit in PATCH_SWITCH2
	rjmp	INTRX_SEXIT
INTRX_S1:
	cpi	r17, 1
	brne	INTRX_S2
	bld	r26, SW_OSCB_OCT	; Set bit in PATCH_SWITCH2
	rjmp	INTRX_SEXIT
INTRX_S2:
	cpi	r17, 2
	brne	INTRX_S3
	bld	r26, SW_OSCB_ENABLE	; Set bit in PATCH_SWITCH2
	rjmp	INTRX_SEXIT
INTRX_S3:
	cpi	r17, 3
	brne	INTRX_S4
	bld	r26, SW_OSCB_WAVE	; Set bit in PATCH_SWITCH2
	rjmp	INTRX_SEXIT
INTRX_S4:
	cpi	r17, 4
	brne	INTRX_S5
	bld	r26, SW_SUSTAIN		; Set bit in PATCH_SWITCH2
; set update_env_dca & update_env_dcf flags
	lds	r27, MIDI_TASK_UPDATE
	ori	R27, (1<<UPDATE_ENV_DCF) | (1<< UPDATE_ENV_DCA)
	sts	MIDI_TASK_UPDATE, r27
	rjmp	INTRX_SEXIT
INTRX_S5:
	cpi	r17, 5
	brne	INTRX_S6
	bld	r26, SW_OSCA_NOISE	; Set bit in PATCH_SWITCH2
	rjmp	INTRX_SEXIT
INTRX_S6:
	cpi	r17, 6
	brne	INTRX_S7
	bld	r26, SW_PWM_SWEEP	; Set bit in PATCH_SWITCH2
	rjmp	INTRX_SEXIT
INTRX_S7:
	bld	r26, SW_OSCA_WAVE	; Set bit in PATCH_SWITCH2

INTRX_SEXIT:				; Finished switch scan, store updated switch bytes
	sts	PATCH_SWITCH2, r26
	rjmp	INTRX_CCEND

; - - - - - - - - - - - - - - - - - - - - - - - - - - - - - - - - - - - - - -

INTRX_SWITCH1:
; r16 parameter value = switch state: 0..63=off, 64..127=on
; r17 contoller# = switch
	cbr	r17, $f8		; Clear highest 5 bits, leaving switch 0..7
	lds	r26, PATCH_SWITCH1
	bst	r16, 6			; load MSB of MIDI CC value into SREG T bit

	cpi	r17, 0
	brne	INTRX_SW1
	bld	r26, SW_KNOB_SHIFT	; Set bit in PATCH_SWITCH1
	rjmp	INTRX_SWEXIT
INTRX_SW1:
	cpi	r17, 1
	brne	INTRX_SW2
	bld	r26, SW_OSC_FM		; Set bit in PATCH_SWITCH1
	rjmp	INTRX_SWEXIT
INTRX_SW2:
	cpi	r17, 2
	brne	INTRX_SW3
	bld	r26, SW_LFO_RANDOM	; Set bit in PATCH_SWITCH1
	rjmp	INTRX_SWEXIT
INTRX_SW3:
	cpi	r17, 3
	brne	INTRX_SW4
	bld	r26, SW_LFO_WAVE	; Set bit in PATCH_SWITCH1
	rjmp	INTRX_SWEXIT
INTRX_SW4:
	cpi	r17, 4
	brne	INTRX_SW5
	bld	r26, SW_FILTER_MODE	; Set bit in PATCH_SWITCH1
	rjmp	INTRX_SWEXIT
INTRX_SW5:
	cpi	r17, 5
	brne	INTRX_SW6
	bld	r26, SW_DISTORTION	; Set bit in PATCH_SWITCH1
	rjmp	INTRX_SWEXIT
INTRX_SW6:
	cpi	r17, 6
	brne	INTRX_SW7
	bld	r26, SW_LFO_ENABLE	; Set bit in PATCH_SWITCH1
	rjmp	INTRX_SWEXIT
INTRX_SW7:
	bld	r26, SW_LFO_DEST	; Set bit in PATCH_SWITCH1

INTRX_SWEXIT:				; Finished switch scan, store updated switch bytes
	sts	PATCH_SWITCH1, r26
	rjmp	INTRX_CCEND

; - - - - - - - - - - - - - - - - - - - - - - - - - - - - - - - - - - - - - -

INTRX_SW_EXT:
	subi	r17, $50		; MIDI CC # --> switch offset 0..15
	cpi	r17, $08
	BRLO	INTRX_SWITCH3		; Jump to Switch 1 if switch 0..7 selected.

INTRX_SWITCH4:
; r16 parameter value = switch state: 0..63=off, 64..127=on
; r17 contoller# = switch
	cbr	r17, $f8		; Clear highest 5 bits, leaving switch 0..7
	lds	r26, PATCH_SWITCH4
	bst	r16, 6			; load MSB of MIDI CC value into SREG T bit

	cpi	r17, 0
	brne	INTRX_SW41
	bld	r26, SW_USER_4_0	; Set bit in PATCH_SWITCH4
	rjmp	INTRX_SW4EXIT
INTRX_SW41:
	cpi	r17, 1
	brne	INTRX_SW42
	bld	r26, SW_USER_4_1	; Set bit in PATCH_SWITCH4
	rjmp	INTRX_SW4EXIT
INTRX_SW42:
	cpi	r17, 2
	brne	INTRX_SW43
	bld	r26, SW_ARP_ENABLE	; Set bit in PATCH_SWITCH4
	rjmp	INTRX_SW4EXIT
INTRX_SW43:
	cpi	r17, 3
	brne	INTRX_SW44
	bld	r26, SW_ARP_REPEAT	; Set bit in PATCH_SWITCH4
	rjmp	INTRX_SW4EXIT
INTRX_SW44:
	cpi	r17, 4
	brne	INTRX_SW45
	bld	r26, SW_USER_4_4	; Set bit in PATCH_SWITCH4
	rjmp	INTRX_SW4EXIT
INTRX_SW45:
	cpi	r17, 5
	brne	INTRX_SW46
	bld	r26, SW_USER_4_5	; Set bit in PATCH_SWITCH4
	rjmp	INTRX_SW4EXIT
INTRX_SW46:
	cpi	r17, 6
	brne	INTRX_SW47
	bld	r26, SW_LFO2_WAVE	; Set bit in PATCH_SWITCH4
	rjmp	INTRX_SW4EXIT
INTRX_SW47:
	bld	r26, SW_LFO2_RANDOM	; Set bit in PATCH_SWITCH4

INTRX_SW4EXIT:				; Finished switch scan, store updated switch bytes
	sts	PATCH_SWITCH4, r26
	rjmp	INTRX_CCEND

; - - - - - - - - - - - - - - - - - - - - - - - - - - - - - - - - - - - - - -

INTRX_SWITCH3:
; r16 parameter value = switch state: 0..63=off, 64..127=on
; r17 contoller# = switch
	cbr	r17, $f8		; Clear highest 5 bits, leaving switch 0..7
	lds	r26, PATCH_SWITCH3
	bst	r16, 6			; load MSB of MIDI CC value into SREG T bit

	cpi	r17, 0
	brne	INTRX_SW31
	bld	r26, SW_MIX_RING	; Set bit in PATCH_SWITCH3
	rjmp	INTRX_SW3EXIT
INTRX_SW31:
	cpi	r17, 1
	brne	INTRX_SW32
	bld	r26, SW_VELOCITY	; Set bit in PATCH_SWITCH3
	rjmp	INTRX_SW3EXIT
INTRX_SW32:
	cpi	r17, 2
	brne	INTRX_SW33
	bld	r26, SW_DCA_MODE	; Set bit in PATCH_SWITCH3
	rjmp	INTRX_SW3EXIT
INTRX_SW33:
	cpi	r17, 3
	brne	INTRX_SW34
	bld	r26, SW_DCA_OPEN	; Set bit in PATCH_SWITCH3
	rjmp	INTRX_SW3EXIT
INTRX_SW34:
	cpi	r17, 4
	brne	INTRX_SW35
	bld	r26, SW_TRANSPOSE	; Set bit in PATCH_SWITCH3
	rjmp	INTRX_SW3EXIT
INTRX_SW35:
	cpi	r17, 5
	brne	INTRX_SW36
	bld	r26, SW_MODWHEEL_ENA	; Set bit in PATCH_SWITCH3
	rjmp	INTRX_SW3EXIT
INTRX_SW36:
	cpi	r17, 6
	brne	INTRX_SW37
	bld	r26, SW_LFO_KBD_SYNC	; Set bit in PATCH_SWITCH3
	rjmp	INTRX_SW3EXIT
INTRX_SW37:
	bld	r26, SW_DCF_KBD_TRACK	; Set bit in PATCH_SWITCH24

INTRX_SW3EXIT:				; Finished switch scan, store updated switch bytes
	sts	PATCH_SWITCH3, r26
	rjmp	INTRX_CCEND

; - - - - - - - - - - - - - - - - - - - - - - - - - - - - - - - - - - - - - -

INTRX_SAVE:
; Save all other controllers
; r16 parameter  value
; r17 contoller#
	ldi	r26, low(MIDICC)
	ldi	r27, high(MIDICC)
	add	r26, r17
	adc	r27, zero
	lsl	r16			; shift MIDI data to 0..254 to match knob value
	st	x, r16			; store in MIDI CC table

; for midi controller CC14 do a special processing
	cpi	r17, $0E	 	; CC14 LFO2FREQ
	breq	INTRX_LFO2FREQ		; update PULSE_KNOB

; for midi controllers CC22..CC30 do a special processing
	cpi	r17, $16		; CC22 DCF_ATTACKTIME
	brlo	INTRX_CCLOW
	breq	INTRX_DCF_ATTACK	; update filter attack time
	cpi	r17, $1A		; CC26 DCA_ATTACKTIME
	brlo	INTRX_DCF_DECAY		; update filter decay time
	breq	INTRX_AMP_ATTACK	; update amplifier attack time
	cpi	r17, $1E		; CC30
	brcc	INTRX_CCHIGH

INTRX_AMP_DECAY:			; update amplifier decay time
	ldi	r17, 4			; CC27..29 -> knob 4 AMP_DECAY
	rjmp	INTRX_UPD_KNOB

INTRX_AMP_ATTACK:
	sts	KNOB_AMP_ATTACK, r16	; sync with ATTACKTIME
	ldi	r17, 5			; CC26 DCA_ATTACKTIME -> knob 5 AMP_ATTACK
	rjmp	INTRX_UPD_KNOB

INTRX_DCF_DECAY:
	ldi	r17, 2			; CC23..25 -> knob 2 FLT_DECAY
	rjmp	INTRX_UPD_KNOB

INTRX_DCF_ATTACK:
	sts	KNOB_DCF_ATTACK, r16	; sync with ATTACKTIME2
	ldi	r17, 3			; CC22 DCF_ATTACKTIME -> knob 3 FLT_ATTACK
	rjmp	INTRX_UPD_KNOB

INTRX_LFO2FREQ:
	sts	PULSE_KNOB, r16		; sync with LFO2FREQ
	ldi	r17, 6			; CC18 LFO2FREQ -> knob 6 KNOB_PULSE

INTRX_UPD_KNOB:
; after midi cc update for the alternative knobs also
; update the primary knob status and setup their OLD_ADC value
	ldi	r26, low(ADC_0)		; get current adc value
	ldi	r27, high(ADC_0)
	add	r26, r17
	adc	r27, zero
	ld	r16, x			; Fetch ADC_X into r16

	ldi	r26, low(OLD_ADC_0)	; update old adc value with current adc value
	ldi	r27, high(OLD_ADC_0)
	add	r26, r17
	adc	r27, zero
	st	x, r16			; Store ADC_X in OLD_ADC_X

	ldi	r26, low(KNOB0_STATUS)
	ldi	r27, high(KNOB0_STATUS)
	add	r26, r17
	adc	r27, zero
	ldi	r17, 0
	st	x, r17			; Clear KNOBX_STATUS
	rjmp	INTRX_CCEND

;-------------------------
INTRX_CCLOW:	; midi cc $0E..$15
.if USE_MASTER_VOLUME
	cpi	r17, 0x15		; MASTER_VOLUME
	brne	INTRX_CC3
	push	r16
	lds	r16, MIDI_TASK_UPDATE	; are there any open update tasks?
	ori	r16, (1<<UPDATE_VOLUME)
	sts	MIDI_TASK_UPDATE, r16
	pop	r16
INTRX_CC3:
.endif	; USE_MASTER_VOLUME
	cpi	r17, 0x14		; MIXER_BALANCE
	brne	INTRX_CCEND

; r16 midi cc MIXER_BALANCE value 0..254
; set DCOA_LEVEL, DCOB_LEVEL
	ldi	r17, $FE		; value 0..254 for DCOB volume calcs
	sub	r17, r16		; knob 254..0 for DCOA volume calcs
	cpi	r17, $02
	BRSH	SET_DCOA		; skip if knob value >= 2
	ldi	r17, $0

SET_DCOA:
	sts	DCOA_LEVEL, r17		; Store DCOA level (0..254)

	cpi	r16, $2
	BRSH	SET_DCOB		; skip if knob value >= 2
	ldi	r16, $0
SET_DCOB:
	sts	DCOB_LEVEL, r16		; Store DCOB level(0..254)

;-------------------------
INTRX_CCHIGH:
	; midi parameter $1e..2F
	; currently nothing to do

INTRX_CCEND:
	pop	r27			; reload old contents of r27 and r26
	pop	r26
	rjmp	INTRX_EXIT

;----------------------------------------------------------------------------
; Ex pitch bender:
INTRX_PBEND:
	cpi	r17, 0xE0		; \
	breq	INTRX_PB1		;  \
	cpi	r17, 0xE1		;  / pitch bend
	breq	INTRX_PB2		; /
	rjmp	INTRX_EXIT

INTRX_PB1:
	inc	r17			; \
	sts	MIDIPHASE, r17		; / MIDIPHASE = 0xE1
	sts	MIDIDATA0, r16		; MIDIDATA0 = dFine  0..127
	rjmp	INTRX_EXIT

INTRX_PB2:
	dec	r17			; \
	sts	MIDIPHASE, r17		; / MIDIPHASE = 0xE0
	lds	r17, MIDIDATA0		; \
	lsl	r17			; / r17 = dFine*2	0..254
	lsl	r17			; \ r16:r17 = P.B.data
	rol	r16			; / 0..255,996
	subi	r16, 128		; r16:r17 = -128,000..+127,996
	sts	MIDIPBEND_L, r17	; \
	sts	MIDIPBEND_H, r16	; / store P.BEND value
	rjmp	INTRX_EXIT

INTRX_EXIT:
	pop	r17
	pop	r16			; \
	out	SREG, r16		; / pop SREG
	pop	r16
	sbi	UCSRB, RXCIE		; RXCIE=1
	reti

.if USE_SERIAL_OUT
;----------------------------------------------------------------------------
; UART transmitter (MIDI_OUT)
;----------------------------------------------------------------------------

UART_UDRE:
	push	r16
	in	r16, SREG		; \
	push	r16			; / push SREG
	cbi	UCSRB, UDRIE		; disable UART interrupt
	sei				; enable other interrupts

	push	r17
	push	r30			; ZL poiter to tables
	push	r31			; ZH

	; if ( UART_TxHead != UART_TxTail)
	lds	r17, UART_TxHead
	lds	r16, UART_TxTail
	cp	r17, r16
	breq	INTTX_EXIT		;  tx buffer empty, don#t enable uart interrupt

	; calculate and store new buffer index
	; tmptail = (UART_TxTail + 1) & UART_TX_BUFFER_MASK;
	lds	r30, UART_TxTail
	subi	r30, -1
	andi	r30, UART_TX_BUFFER_MASK

	; UART_TxTail = tmptail;
	sts	UART_TxTail, r30

	; get one byte from buffer and write it to UART
	; UART0_DATA = UART_TxBuf[tmptail]
	; start transmitter
	ldi	r31, 0x00
	subi	r30, LOW( -UART_TxBuf)
	sbci	r31, HIGH( -UART_TxBuf)
	ld	r16, Z
	out	UDR, r16

	; disable global interrupt,
	; so we can leave this service routine properly
	cli
	sbi	UCSRB, UDRIE		; enable uart interrupt

INTTX_EXIT:
	pop	r31
	pop	r30
	pop	r17
	pop	r16			; \
	out	SREG, r16		; / pop SREG
	pop	r16
	reti
.endif	; USE_SERIAL_OUT

;----------------------------------------------------------------------------
;	M A I N   L E V E L   S U B R O U T I N E S
;----------------------------------------------------------------------------

.if USE_DEBUG_OUT
;	.nolist
	.include "debug_uart.inc"
;	.list
.endif	; USE_DEBUG_OUT

;----------------------------------------------------------------------------
; initialize UART
;----------------------------------------------------------------------------

	.equ	midi_ubrr_val   = ((cpu_frequency+midi_baud_rate*8)/(midi_baud_rate*16)-1)	; smart rounding
	.equ	midi_baud_real  = (cpu_frequency/(16*(midi_ubrr_val+1)))					; real baudrate
	.equ	midi_baud_error = ((midi_baud_real*1000)/midi_baud_rate-1000)				; error in promille

.if ((midi_baud_error>10) || (midi_baud_error<-10))							; max. +/-10 promille error
  .error "MIDI baudrate error greater than 1 percent, too high!"
.endif

uart_init:
	; set midi frequency 31250 Hz (32us)
	ldi	r16, high( midi_ubrr_val) & ~(1<<URSEL)
	out	UBRRH, r16
	ldi	r16, low( midi_ubrr_val)
	out	UBRRL, r16

.if USE_SERIAL_OUT
; enable transmitter, receiver and receiver interrupt
	ldi	r16, (1<<TXEN)|(1<<RXCIE)|(1<<RXEN)
	out	UCSRB, r16
.else
; enable receiver and receiver interrupt
	ldi	r16, (1<<RXCIE)|(1<<RXEN)	; \
	out	UCSRB, r16			; / RXCIE=1, RXEN=1
.endif	; USE_SERIAL_OUT
	ret

.if USE_SERIAL_OUT
;----------------------------------------------------------------------------
;
;----------------------------------------------------------------------------
; r16 character to send
; r17 tmphead
; r18 UART_TxTail
; r31:r30 pointer to transmitter buffer

uart_putc:
	push	r17
	push	r18
	push	r30			; ZL poiter to tables
	push	r31			; ZH

	; tmphead  = (UART_TxHead + 1) & UART_TX_BUFFER_MASK;
	lds	r17, UART_TxHead
	subi	r17, -1
	andi	r17, UART_TX_BUFFER_MASK

	; while ( tmphead == UART_TxTail)
	; wait for free space in buffer
uart_putc_wait:
	lds	r18, UART_TxTail
	cp	r17, r18		; tmphead == UART_TxTail
	breq	uart_putc_wait

	; UART_TxBuf[tmphead] = data;
	mov	r30, r17
	ldi	r31, 0x00
	subi	r30, LOW( -UART_TxBuf)
	sbci	r31, HIGH( -UART_TxBuf)
	st	Z, r16

	sts	UART_TxHead, r17	; UART_TxHead = tmphead;
	sbi	UCSRB, UDRIE		; enable UDRE interrupt, start transmitter

	pop	r31
	pop	r30
	pop	r18
	pop	r17
	ret

tx_buf_empty:
	push	r17
	; if ( UART_TxHead == UART_TxTail)
	lds	r17, UART_TxHead
	lds	r16, UART_TxTail
	cp	r17, r16
	ldi	r16, 0xff		; empty
	breq	tx_buf_is_empty
	ldi	r16, 0x00		; not empty
tx_buf_is_empty:
	pop	r17
	ret				; 0: not empty, -1: empty
.endif	; USE_SERIAL_OUT

;----------------------------------------------------------------------------
; send midi cc message
;----------------------------------------------------------------------------
;  r16 cc param
;  r17 cc value

.if USE_SERIAL_OUT | USE_DEBUG_OUT

send_midi_cc:
 .if USE_SERIAL_OUT
 	push	r16
 	lds	r16, CONTROL_STATE
 	andi	r16, (1<<ENABLE_MIDI_CC_OUT)
 	pop	r16
 	breq	send_midi_cc_exit

	push	r17			; save cc value
	push	r16			; save cc param

	ldi	r16, 0xB0		; control change
	rcall	uart_putc
	pop	r16			; get cc param
	rcall	uart_putc		; cc param
	pop	r16			; get cc value
	rcall	uart_putc		; cc value
	ret
send_midi_cc_exit:
 .endif	; USE_SERIAL_OUT

 .if USE_DEBUG_OUT
 	push	r16
 	lds	r16, CONTROL_STATE
 	andi	r16, (1<<ENABLE_DEBUG_OUT)
 	pop	r16
 	breq	debug_out_exit

	rcall	debug_entry		; open for send midi cc

	rcall	debug_uart_write_byte	; cc param
	ldi	r16, ' '		; print blank
	rcall	debug_uart_transmit
	mov	r16, r17
	rcall	debug_uart_write_byte	; cc value

	rcall	debug_uart_write_crlf
	rcall	debug_exit
	ret
debug_out_exit:
 .endif	 ; USE_DEBUG_OUT

	ret

.endif	; USE_SERIAL_OUT || USE_DEBUG_OUT

;=============================================================================
;	Delay subroutines
;=============================================================================

WAIT_10US:
	push	r16			; 3+2
	ldi	r16, 50			; 1

W10U_LOOP:
	dec	r16			; 1\
	brne	W10U_LOOP		; 2/1 / 49*3 + 2
	pop	r16			; 2
	ret				; 4

;=============================================================================
;	I/O subroutines
;=============================================================================

;----------------------------------------------------------------------------
; A/D conversion (start)
; - - - - - - - - - - - - - - - - - - - - - - - - - - - - - - - - - - - - - -
; In:	r18 = channel #	0..7
; Out:   -
; Used:  -
;----------------------------------------------------------------------------
ADC_START:
	out	ADMUX, r18		; set multiplexer
	sbi	ADCSRA, 6		; ADSC=1
	ret

;----------------------------------------------------------------------------
; A/D conversion (end)
; - - - - - - - - - - - - - - - - - - - - - - - - - - - - - - - - - - - - - -
; In:	-
; Out:	r16 = result		0..255
; Used:	SREG, r17
;----------------------------------------------------------------------------
ADC_END:
ADCE_LOOP:
	sbis	ADCSRA, 4		; \
	rjmp	ADCE_LOOP		; / wait for ADIF==1
	sbi	ADCSRA, 4		; clear ADIF
	in	r16, ADCL		; \
	in	r17, ADCH		; / r17:r16 = 000000Dd:dddddddd
	lsr	r17			; \
	ror	r16			; / r17:r16 = 0000000D:dddddddd
	lsr	r17			; \
	ror	r16			; / r16 = Dddddddd
	ret

;=============================================================================
;	arithmetic subroutines
;=============================================================================

;----------------------------------------------------------------------------
; 16 bit arithmetical shift right (division by 2^n)
; - - - - - - - - - - - - - - - - - - - - - - - - - - - - - - - - - - - - - -
; In:	r17:r16 = x
;	r18 = n (shift count)	0..16
; Out:	r17:r16 = x asr n
; Used:	SREG
;----------------------------------------------------------------------------
ASR16:
	tst	r18
	breq	ASR16_EXIT
	push	r18

ASR16_LOOP:
	asr	r17			; \
	ror	r16			; / r17:r16 = r17:r16 asr 1
	dec	r18
	brne	ASR16_LOOP
	pop	r18

ASR16_EXIT:
	ret

;----------------------------------------------------------------------------
; 32 bit logical shift right
; - - - - - - - - - - - - - - - - - - - - - - - - - - - - - - - - - - - - - -
; In:	r19:r18:r17:r16 = x
;	r20 = n (shift count)
; Out:	r19:r18:r17:r16 = x >> n
; Used:	SREG
;----------------------------------------------------------------------------
SHR32:
	tst	r20
	breq	SHR32_EXIT
	push	r20

SHR32_LOOP:
	lsr	r19
	ror	r18
	ror	r17
	ror	r16
	dec	r20
	brne	SHR32_LOOP
	pop	r20

SHR32_EXIT:
	ret

;----------------------------------------------------------------------------
; 32 bit logical shift left
; - - - - - - - - - - - - - - - - - - - - - - - - - - - - - - - - - - - - - -
; In:	r19:r18:r17:r16 = x
;	r20 = n (shift count)
; Out:	r19:r18:r17:r16 = x << n
; Used:	SREG
;----------------------------------------------------------------------------
SHL32:
	tst	r20
	breq	SHL32_EXIT
	push	r20

SHL32_LOOP:
	lsl	r16
	rol	r17
	rol	r18
	rol	r19
	dec	r20
	brne	SHL32_LOOP
	pop	r20

SHL32_EXIT:
	ret

;----------------------------------------------------------------------------
; 8 bit x 8 bit multiplication (unsigned)
; - - - - - - - - - - - - - - - - - - - - - - - - - - - - - - - - - - - - - -
; In:	r16 = x			0..255
;	r17 = y			0,000..0,996
; Out:	r17:r16 = x * y		0,000..254,004
; Used:	SREG, r18-r20
;----------------------------------------------------------------------------
MUL8X8U:

	MUL	r16, r17
	movw	r16, r0
	ret

;----------------------------------------------------------------------------
; 32 bit x 16 bit multiplication (unsigned)
; - - - - - - - - - - - - - - - - - - - - - - - - - - - - - - - - - - - - - -
; In:	r19:r18:r17:r16 = x		0..2^32-1
;	r23:r22 = y			0,yyyyyyyyyyyyyyyy  0..0,9999847
; Out:	r19:r18:r17:r16 = x * y	0..2^32-1
; Used:	SREG, r20-r29
;----------------------------------------------------------------------------
MUL32X16:
; multiply with high multiplier x
	mul	r19, r23		; ax
	movw	r29:r28, r1:r0
	mul	r18, r23		; bx
	movw	r21:r20, r1:r0
	mul	r17, r23		; cx
	movw	r27:r26, r1:r0
	mul	r16, r23		; dx
	mov	r25, r0
	add	r26, r1
	adc	r27, r20
	adc	r28, r21
	adc	r29, ZERO
; multiply with low multiplier y
	mul	r19, r22		; ay
	movw	r21:r20, r1:r0
	mul	r17, r22		; cy
	add	r25, r0
	adc	r26, r1
	adc	r27, r20
	adc	r28, r21
	adc	r29, ZERO
	mul	r18, r22		; by
	movw	r21:r20, r1:r0
	mul	r16, r22		; dy
	mov	r24, r0
	add	r25, r1
	adc	r26, r20
	adc	r27, r21
	adc	r28, ZERO
	adc	r29, ZERO

	mov	r16, r26		; \
	mov	r17, r27		;  \
	mov	r18, r28		;  / x * y
	mov	r19, r29		; /

	ret

;----------------------------------------------------------------------------
; Load 32 bit phase value from ROM
; - - - - - - - - - - - - - - - - - - - - - - - - - - - - - - - - - - - - - -
; In:	r30 = index
; Out:	r19:r18:r17:r16 = value
; Used:	SREG, r0, r30:r31
;----------------------------------------------------------------------------
LOAD_32BIT:
	lsl	r30			; r30 *= 2
	ldi	r31, 0
	adiw	r30, DELTA_C		; Z = ROM address
	add	r30, r30
	adc	r31, r31
	lpm	r16, z+
	lpm	r17, z+
	lpm	r18, z+
	lpm	r19, z+
	ret

;----------------------------------------------------------------------------
; Load phase delta from ROM
; - - - - - - - - - - - - - - - - - - - - - - - - - - - - - - - - - - - - - -
; In:	r23:r22 = indexs = 0,0..12,0 = note
;       r20 = 0..11, octave
; Out:	r19:r18:r17:r16 = delta
; Used:	SREG, r0, r21, r24-r31
;----------------------------------------------------------------------------
LOAD_DELTA:
	push	r22
	push	r23
	mov	r30, r23
	rcall	LOAD_32BIT		; load delta value for specified note
	mov	r24, r16
	mov	r25, r17
	mov	r26, r18
	mov	r27, r19		; r27-r24 = delta[n]
	mov	r30, r23
	inc	r30			; next note
	rcall	LOAD_32BIT		; load delata value for specified note
	sub	r16, r24
	sbc	r17, r25
	sbc	r18, r26		; r27-r24 = delta[n+1]
	sbc	r19, r27		; r19-r16 = delta[n+1]-delta[n]
	push	r24			; save delta[n]
	push	r25
	push	r26
	push	r27
	mov	r23, r22
	ldi	r22, 0
	push	r20			; r22 * (delta[n+1]-delta[n])
	rcall	MUL32X16		; r19:r18:r17:r16 = r19:r18:r17:r16 * r23:r22
	pop	r20			; recal delta[n]
	pop	r27
	pop	r26
	pop	r25
	pop	r24
	add	r16, r24		; delta[n] + r22 * (delta[n+1]-delta[n])
	adc	r17, r25
	adc	r18, r26
	adc	r19, r27
	pop	r23
	pop	r22
	ret

;----------------------------------------------------------------------------
; note number recalculation
; - - - - - - - - - - - - - - - - - - - - - - - - - - - - - - - - - - - - - -
; In:	r23 = n		0..139 = m12 + 12*n12
; Out:	r23 = m12	0..11 = note
;	r20 = n12	0..11 = octave
; Used:	SREG
;----------------------------------------------------------------------------
NOTERECALC:
	ldi	r20, 0			; n12 = 0
	rjmp	NRC_2

NRC_1:
	subi	r23, 12			; m12 -= 12
	inc	r20			; n12++

NRC_2:
	cpi	r23, 12
	brsh	NRC_1			; repeat while m12 >= 12
	ret

;----------------------------------------------------------------------------
; read a byte from a table
; - - - - - - - - - - - - - - - - - - - - - - - - - - - - - - - - - - - - - -
; In:	r16 = i		0..255
;	r31:r30 = &Tab
; Out:	r16 = Tab[i]	0..255
; Used:	SREG, r30:r31
;----------------------------------------------------------------------------
TAB_BYTE:
	add	r30, r30		; \
	adc	r31, r31		; / Z = 2 * &Tab
	add	r30, r16
	adc	r31, ZERO
	lpm	r16, z
	ret

;----------------------------------------------------------------------------
; read a word from a table
; - - - - - - - - - - - - - - - - - - - - - - - - - - - - - - - - - - - - - -
; In:	r16 = i			0..255
;	r31:r30 = &Tab
; Out:	r19:r18 = Tab[i]	0..65535
; Used:	SREG, r0, r30:r31
;----------------------------------------------------------------------------
TAB_WORD:
	add	r30, r16
	adc	r31, ZERO
	add	r30, r30		; \
	adc	r31, r31		; / Z = 2 * &Tab
	lpm	r18, z+			; LSByte
	lpm	r19, z			; MSByte
	ret

;----------------------------------------------------------------------------
; "time" --> "rate" conversion
; - - - - - - - - - - - - - - - - - - - - - - - - - - - - - - - - - - - - - -
; In:	r16 = time			0..255
; Out:	r19:r18:r17:r16 = rate		0x001B0000..0xFFFF0000
; Used:	SREG, r0, r30:r31
;----------------------------------------------------------------------------
ADCTORATE:
.if !USE_TIMETORATE_64 && !USE_TIMETORATE_128
 .if !USE_TIMETORATE_128
	lsr	r16
 .endif	; !USE_TIMETORATE_128
	lsr	r16
.endif	; !USE_TIMETORATE_64 && !USE_TIMETORATE_128
	lsr	r16			; 0..31
	ldi	r30, low( TIMETORATE)
	ldi	r31, high(TIMETORATE)
	rcall	TAB_WORD		; r19:r18 = rate
	clr	r16
	clr	r17
	ret

;----------------------------------------------------------------------------
; conversion of the "detune B" potentiometer function
; - - - - - - - - - - - - - - - - - - - - - - - - - - - - - - - - - - - - - -
; In:	r16 = x		0..255
; Out:	r17:r16 = y	0,000..255,996
; Used:	SREG, r18, r22, r23, r30, r31
;----------------------------------------------------------------------------
NONLINPOT:
	ldi	r22, 0
	mov	r23, r16
	cpi	r23, 112
	brlo	NLP_I
	cpi	r23, 144
	brlo	NLP_II
	rjmp	NLP_III

NLP_I:
	ldi	r16, 0			; \  r18:r17:r16 = m =
	ldi	r17, 32			;  > = 126/112 =
	ldi	r18, 1			; /  = 1,125
	ldi	r30, 0			; \ r31:r30 = n =
	ldi	r31, 0			; / = 0,0
	rjmp	NLP_CONT

NLP_II:
	ldi	r16, 8			; \  r18,:r17:r16 = m =
	ldi	r17, 33			;  > = (130-126)/(143-112) =
	ldi	r18, 0			; /  = 0,129032258
	ldi	r30, 140		; \ r31:r30 = n =
	ldi	r31, 111		; / = 126 - m*112 = 111,5483871
	rjmp	NLP_CONT

NLP_III:
	ldi	r16, 183		; \  r18:r17:r16 = m =
	ldi	r17, 29			;  > = (255-130)/(255-143) =
	ldi	r18, 1			; /  = 1,116071429
	ldi	r30, 103		; \ r31:r30 = n =
	ldi	r31, 226		; / 255 - m*255 = -29,59821429

NLP_CONT:
	ldi	r19, 0
	rcall	MUL32X16		; r19:r18:r17:r16 = r19:r18:r17:r16 * r23:r22
	add	r16, r30
	adc	r17, r31
	ret

;----------------------------------------------------------------------------
; Write byte to eeprom memory
; - - - - - - - - - - - - - - - - - - - - - - - - - - - - - - - - - - - - - -
; In:	r16	= value		0..255
;	r18:r17 = eeprom memory address
; Used:	r16, r17, r18
;----------------------------------------------------------------------------
EEPROM_WRITE:
					; Wait for completion of previous write
	sbic	EECR, EEWE
	rjmp	EEPROM_write		; loop until eeprom is ready
	in	temp_SREG, SREG		; save SREG
	cli				; disable interrupts during timed eeprom sequence
	out	EEARH, r18
	out	EEARL, r17		; single byte offset from WRITE_OFFSET
	out	EEDR,  r16		; Write data (r16) to data register
	sbi	EECR, EEMWE		; Write logical one to EEMWE
	sbi	EECR, EEWE		; Start eeprom write by setting EEWE
	out	SREG, temp_SREG		; restore SREG (restarts interrupts if enabled)
	ret

;----------------------------------------------------------------------------
; Read byte from eeprom memory
; - - - - - - - - - - - - - - - - - - - - - - - - - - - - - - - - - - - - - -
; In:	r18:r17 = eeprom memory address
; Out:	r16	= value  0..255
; Used:	r16, r17, r18
;----------------------------------------------------------------------------
EEPROM_read:

	sbic	EECR, EEWE		; Wait for completion of previous write
	rjmp	EEPROM_read
	in	temp_SREG, SREG		; save SREG
	cli				; disable interrupts during timed eeprom sequence
	out	EEARH, r18		; Set up address (r18:r17) in address register
	out	EEARL, r17
	sbi	EECR, EERE		; Start eeprom read by writing EERE
	in	r16, EEDR		; Read data from data register
	out	SREG, temp_SREG	; restore SREG (restarts interrupts if enabled)
	ret

;----------------------------------------------------------------------------
; Clear knob status
; Set knob status to 'unmoved' and save current knob positions
; - - - - - - - - - - - - - - - - - - - - - - - - - - - - - - - - - - - - - -
; In:	    --
; Out:		--
; Used:	    r16
;----------------------------------------------------------------------------

CLEAR_KNOB_STATUS:			;	set knob status to 'unmoved' and save current knob positions
	clr	r16
	sts	KNOB0_STATUS, r16
	sts	KNOB1_STATUS, r16
	sts	KNOB2_STATUS, r16
	sts	KNOB3_STATUS, r16
	sts	KNOB4_STATUS, r16
	sts	KNOB5_STATUS, r16
	sts	KNOB6_STATUS, r16
	sts	KNOB7_STATUS, r16

	lds	r16, ADC_0		; Save current pot positions for future comparison
	sts	OLD_ADC_0, r16
	lds	r16, ADC_1
	sts	OLD_ADC_1, r16
	lds	r16, ADC_2
	sts	OLD_ADC_2, r16
	lds	r16, ADC_3
	sts	OLD_ADC_3, r16
	lds	r16, ADC_4
	sts	OLD_ADC_4, r16
	lds	r16, ADC_5
	sts	OLD_ADC_5, r16
	lds	r16, ADC_6
	sts	OLD_ADC_6, r16
	lds	r16, ADC_7
	sts	OLD_ADC_7, r16
	ret

;----------------------------------------------------------------------------
; Load patch
; - - - - - - - - - - - - - - - - - - - - - - - - - - - - - - - - - - - - - -
; In:	r16 = patch number
; Out:	Loads 16/48 byte patch into MIDI CC table
; Used:	r16-r19, r28, r29
;----------------------------------------------------------------------------

; r16	patch number
; r17	Low byte of eeprom address
; r18	High byte of eeprom address
; r19	MIDI CC table offset
; r28	\
; r28	/ Y pointer to midi CC
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
